ziteh/LEAP/3D_models/Solidworks/下肢/組合/多圈可變電阻定位齒輪組[01-v1.0].SLDASM

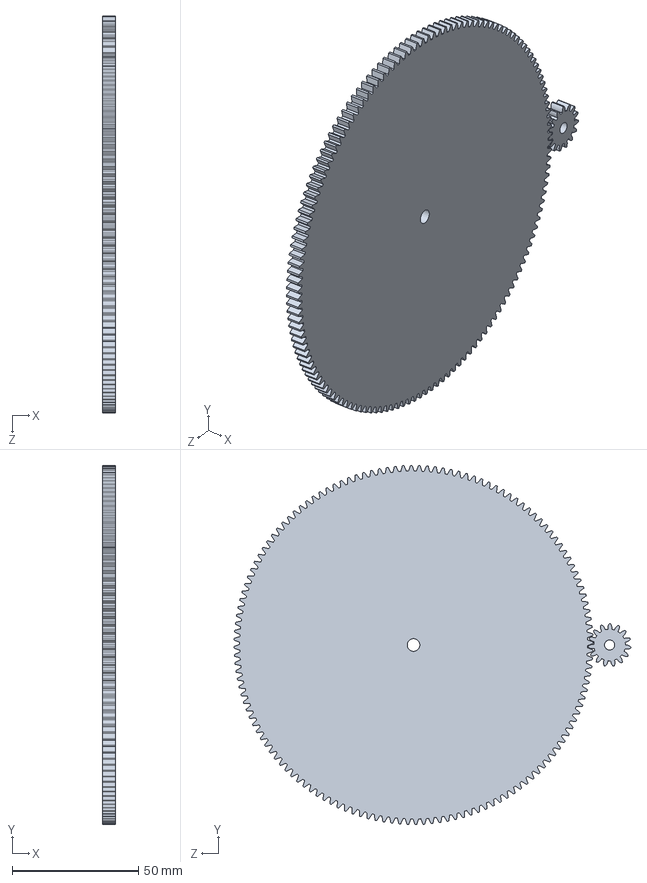
[picture p17: CAD file, 2020-11-13]
3D_models/Solidworks/下肢/組合/多圈可變電阻定位齒輪組[01-v1.0].SLDASM
5.00 x 142.0 x 157.0 mm
spur gear_am x 2
