ziteh/LEAP/3D_models/Solidworks/縮小測試用模型/伺服馬達SG90用轉軸片壓克力固定組合[01-v1.0].SLDASM

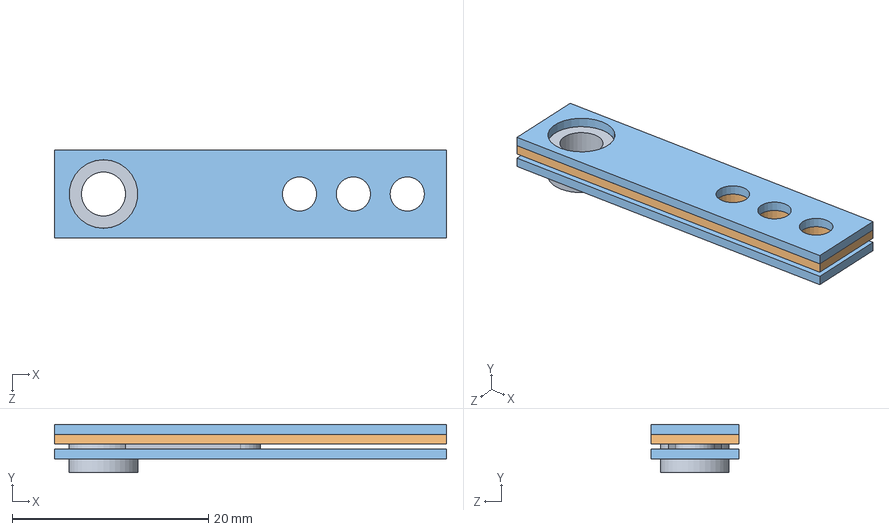
[picture p18: CAD file, 2020-11-13]
3D_models/Solidworks/縮小測試用模型/伺服馬達SG90用轉軸片壓克力固定組合[01-v1.0].SLDASM
40.0 x 4.90 x 9.00 mm
伺服馬達SG90用轉軸片[01-v1.0]
伺服馬達SG90用轉軸片壓克力套[01-v1.0]
伺服馬達SG90用轉軸片壓克力套[02-v1.0] x 2
