ziteh/LEAP/3D_models/Solidworks/下肢/組合/腿部組合-L[01_v3.1(多圈齒輪)].SLDASM

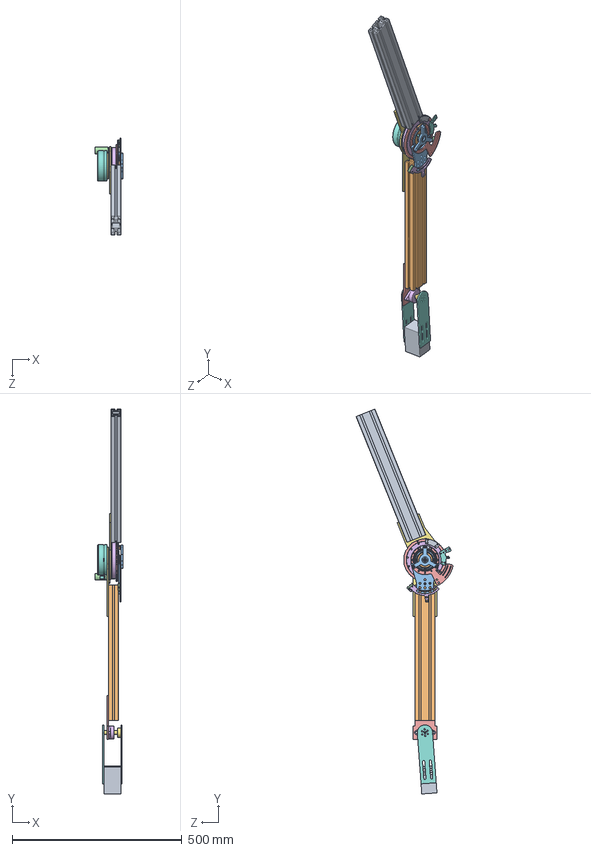
[picture p19: CAD file, 2020-11-13]
3D_models/Solidworks/下肢/組合/腿部組合-L[01_v3.1(多圈齒輪)].SLDASM
81.5 x 1135.4 x 285.7 mm
3060鋁擠型-大腿[01_v1.0]
3060鋁擠型-小腿[01_v1.0]
SHD-2SH_剛性齒輪固定片(01_v2.1)
可變電阻WXD3-13-10KΩ[01-v1.0]
軸承固定座-KFL12固定片[01-v1.0]
軸承固定座-KFL12[01-v1.0]
腳踝軸承軸心固定塊[01_v1.0]
腳踝軸承軸心固定片[01_v1.0] x 2
腳底板固定塊[01_v1.0]
軸承_HD軸向固定(01-v1.0)
HD軸向軸承固定塊(01_v1.0)
HD軸向軸承固定塊(02_v2.0)
多圈可變電阻定位齒輪組-m0.5 250齒[01-v1.0]
多圈可變電阻定位齒輪組-20齒[01-v2.0]
定位多圈可變電阻固定片[01_v5.0]
SHD-2SH_彈性齒杯-可變電阻齒輪固定片[01_v2.0]
SHD-2SH_彈性齒杯-可變電阻齒輪固定片[02_v2.0]
多圈可變電阻定位齒輪固定塊[01-v2.0]
HD軸向軸承固定片(01_v2.0)
微動開關_SS-5GL[01-v1.0] x 2
微動開關(SS-5GL)固定片[01_v2.2]
微動開關(SS-5GL)固定片[02_v2.0]
EC90flot固定片(01_v3.1)
EC90fl-160W-586655
EC90flot軸心固定塊(01_v3.1)
SHD-25-2SH-WG
25 WG BEARING DS
SHD-25-2SH-FS
SHD-25-2SH-CS
SHD-25-2SH-FS2
SHD-2SH_彈性齒杯固定片(01_v4.2)
M4×1[01-v1.0] x 2
HD軸向軸承固定片(03_v1.0)
HD軸向軸承固定片(02_v1.0)
