ziteh/LEAP/3D_models/Solidworks/下肢/組合/氣彈簧組合-01_v1.0.SLDASM

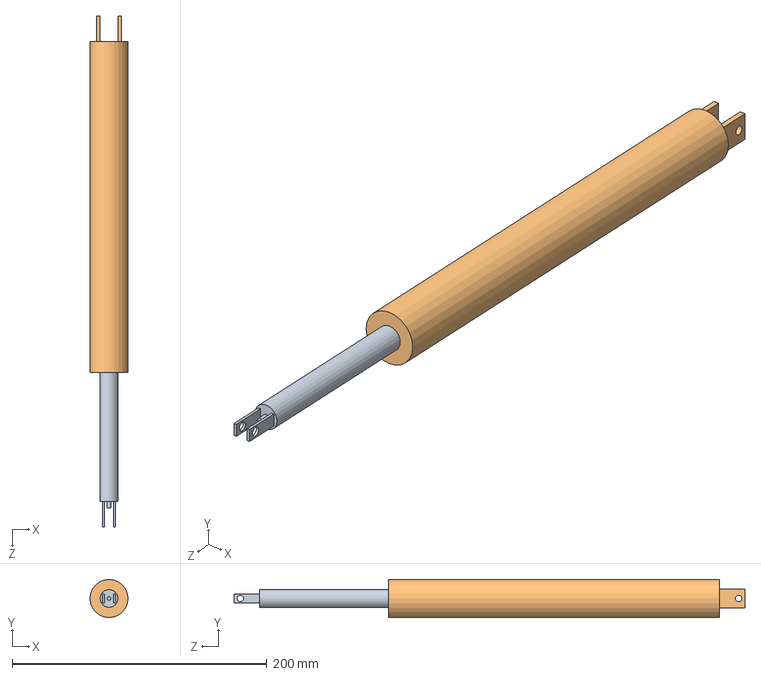
[picture p20: CAD file, 2020-11-13]
3D_models/Solidworks/下肢/組合/氣彈簧組合-01_v1.0.SLDASM
30.0 x 30.0 x 401.6 mm
氣彈簧_伸縮杆-01_v1.0
氣彈簧_缸體-01_v1.0
