ziteh/LEAP/3D_models/Solidworks/下肢/組合/FSR固定片組合[01_v1.0].SLDASM

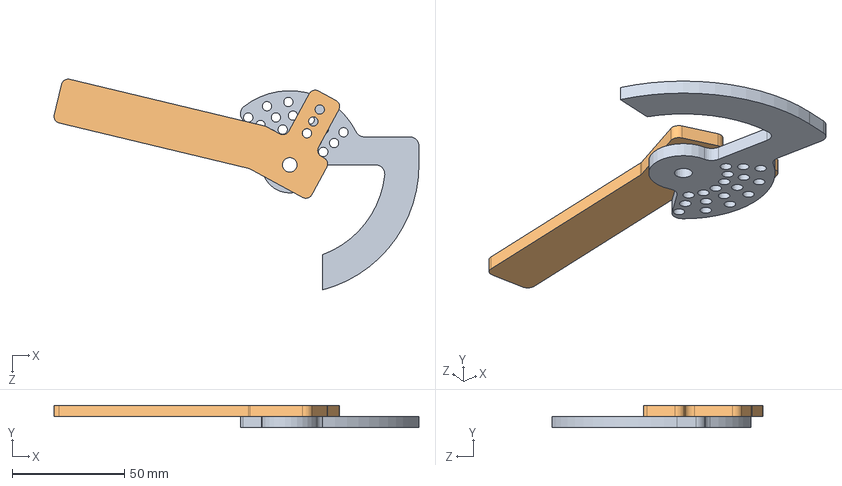
[picture p21: CAD file, 2020-11-13]
3D_models/Solidworks/下肢/組合/FSR固定片組合[01_v1.0].SLDASM
162.4 x 10.0 x 93.8 mm
FSR固定片[02_v4.0]
FSR固定片[01_v4.0]
