ziteh/LEAP/3D_models/Solidworks/縮小測試用模型/定位齒輪[01-v1.0].SLDASM

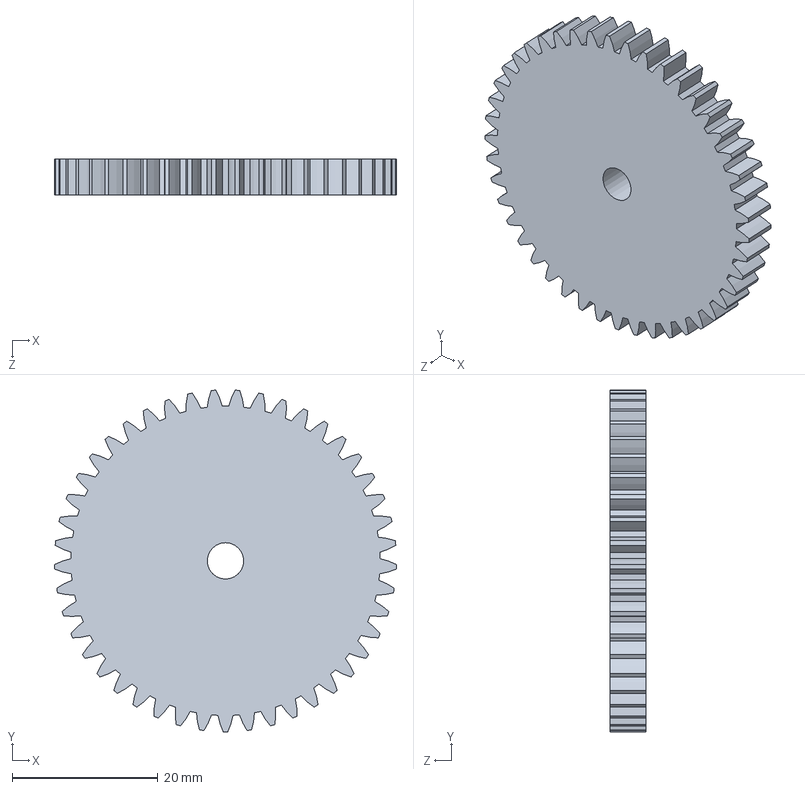
[picture p22: CAD file, 2020-11-13]
3D_models/Solidworks/縮小測試用模型/定位齒輪[01-v1.0].SLDASM
47.0 x 47.0 x 5.00 mm
