ziteh/LEAP/3D_models/Solidworks/下肢/組合/微動開關(SS-5GL)-固定片組合[01_v1.0(伸直)].SLDASM

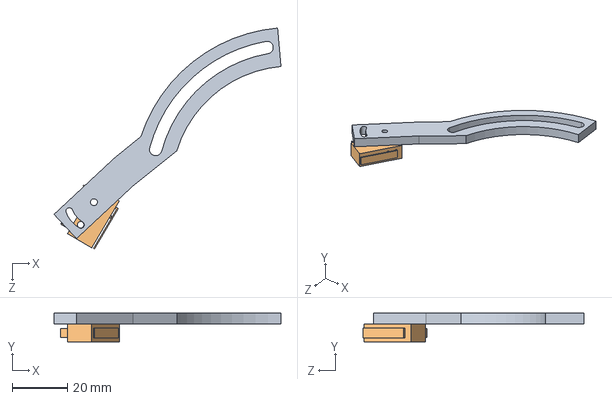
[picture p23: CAD file, 2020-11-13]
3D_models/Solidworks/下肢/組合/微動開關(SS-5GL)-固定片組合[01_v1.0(伸直)].SLDASM
82.4 x 10.4 x 80.2 mm
微動開關(SS-5GL)固定片[01_v1.0]
微動開關_SS-5GL[01-v1.0]
