ziteh/LEAP/3D_models/Solidworks/下肢/組合/諧波減速機(SHF-25-100)組合-01_v1.0.SLDASM

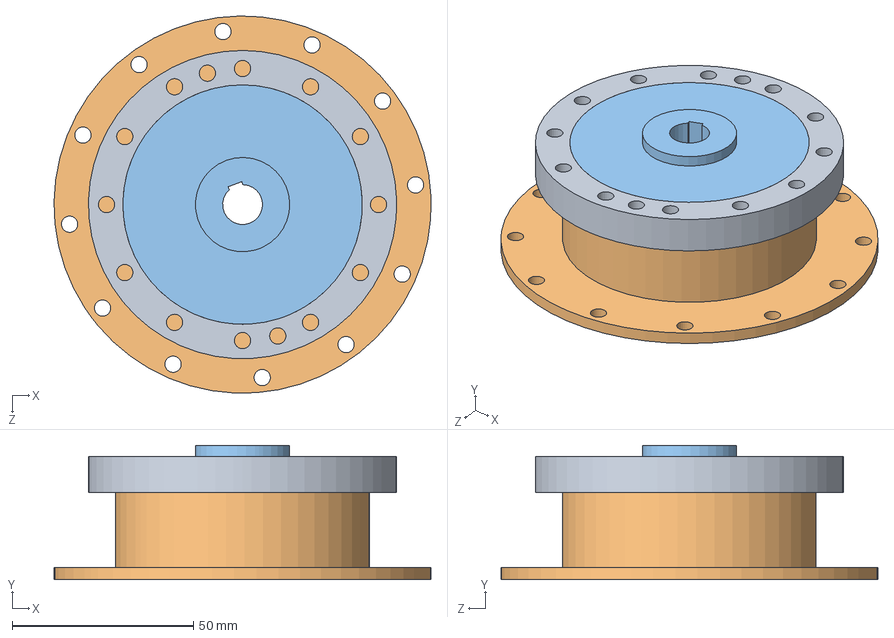
[picture p24: CAD file, 2020-11-13]
3D_models/Solidworks/下肢/組合/諧波減速機(SHF-25-100)組合-01_v1.0.SLDASM
103.9 x 37.0 x 103.9 mm
諧波減速機(SHF-25-100)_剛性齒輪-01_v1.0
諧波減速機(SHF-25-100)_彈性齒杯-01_v1.0
諧波減速機(SHF-25-100)_波產生器-01_v1.0
