ziteh/LEAP/3D_models/Inventor/鋁擠型/3060鋁擠型(Prototype)-01_v1.DXF

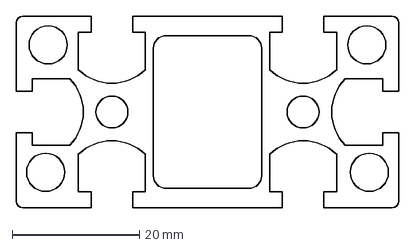
[picture p25: CAD file, 2020-11-13]
3D_models/Inventor/鋁擠型/3060鋁擠型(Prototype)-01_v1.DXF
60.0 x 30.0 mm
