ziteh/LEAP/3D_models/Solidworks/下肢/Others/腳踝部[01-v1.0].SLDPRT

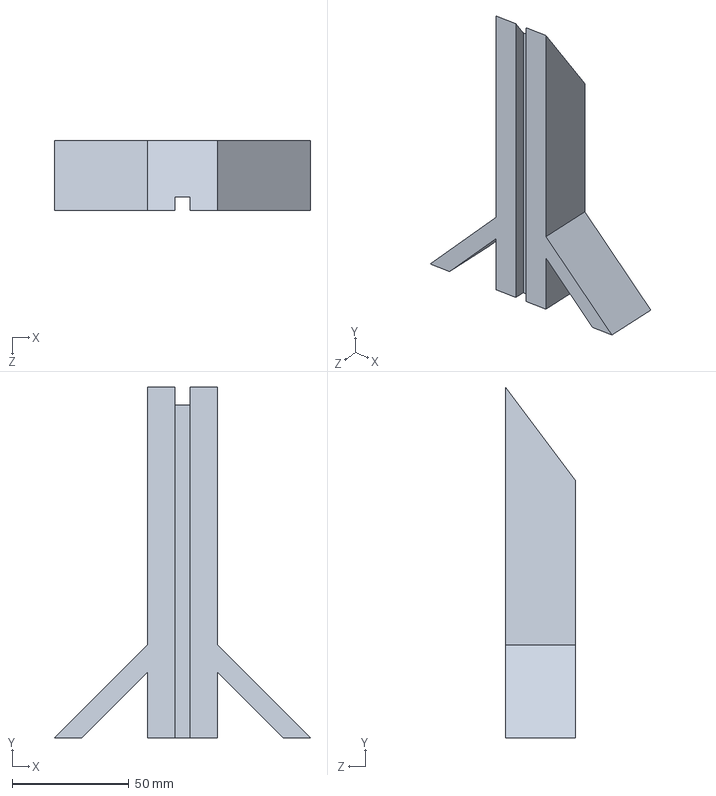
[picture p26: CAD file, 2020-11-14]
3D_models/Solidworks/下肢/Others/腳踝部[01-v1.0].SLDPRT
109.5 x 150.0 x 30.0 mm
