ziteh/LEAP/3D_models/Solidworks/下肢/固定-標準/M4×1[01-v1.0].SLDPRT

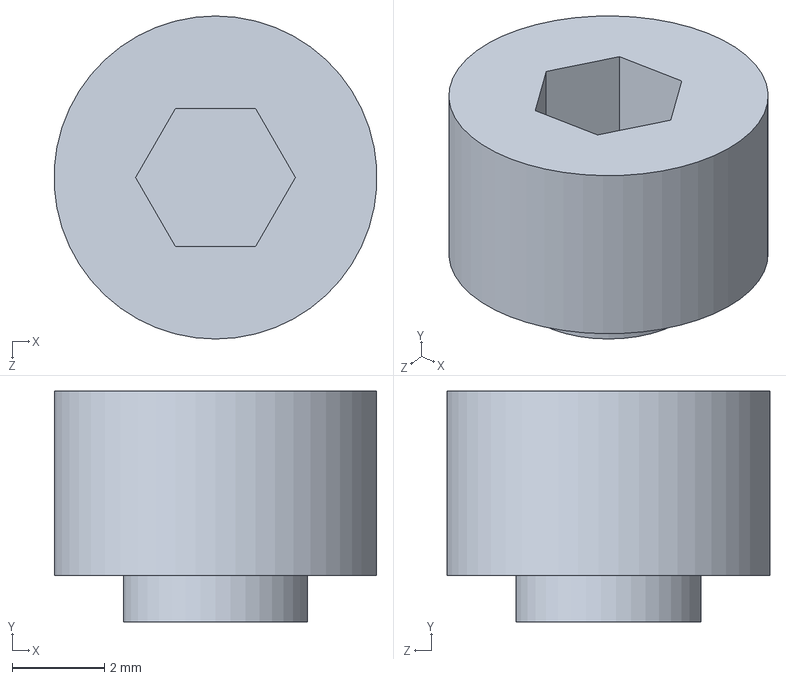
[picture p27: CAD file, 2020-11-14]
3D_models/Solidworks/下肢/固定-標準/M4×1[01-v1.0].SLDPRT
6.99 x 5.00 x 7.00 mm
