ziteh/LEAP/3D_models/Solidworks/下肢/機械/SHD-2SH/SHD-25-2SH-CS.sldprt

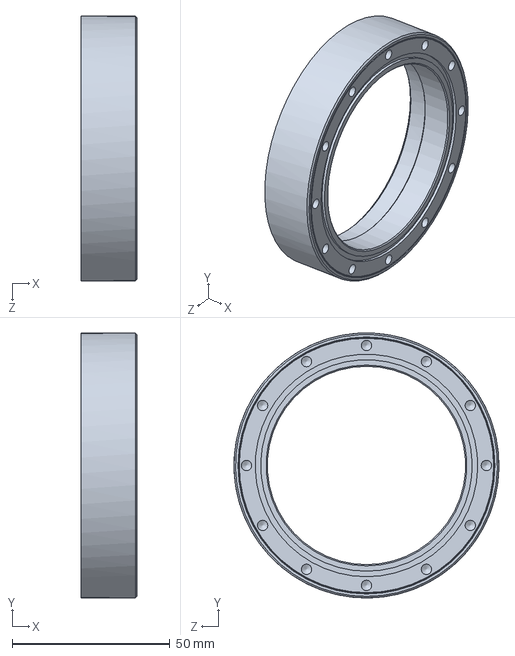
[picture p28: CAD file, 2020-11-14]
3D_models/Solidworks/下肢/機械/SHD-2SH/SHD-25-2SH-CS.sldprt
17.7 x 84.0 x 84.0 mm
