ziteh/LEAP/3D_models/Solidworks/下肢/機械/軸承_HD軸向固定(01-v1.0).SLDPRT

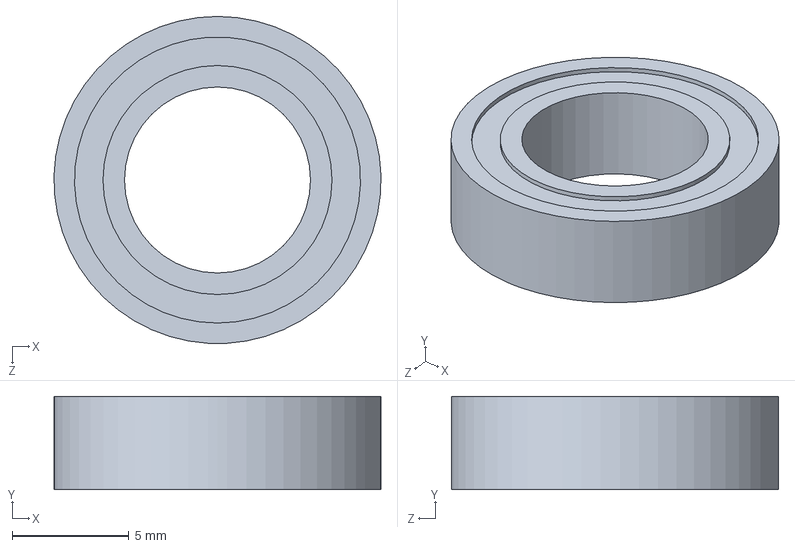
[picture p29: CAD file, 2020-11-14]
3D_models/Solidworks/下肢/機械/軸承_HD軸向固定(01-v1.0).SLDPRT
14.0 x 4.00 x 14.0 mm
