ziteh/LEAP/3D_models/Solidworks/下肢/鋁擠型/3060鋁擠型-大腿[01_v1.0].SLDPRT

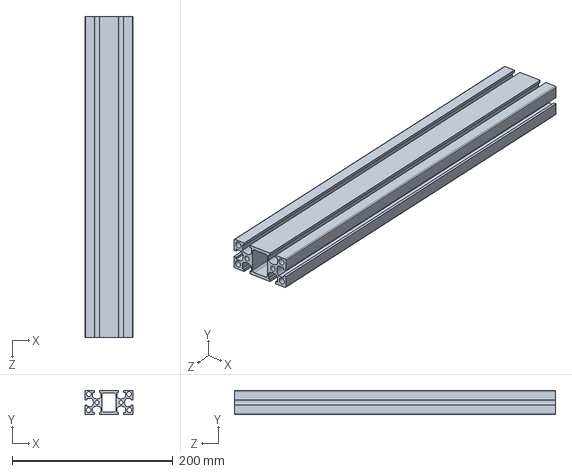
[picture p30: CAD file, 2020-11-14]
3D_models/Solidworks/下肢/鋁擠型/3060鋁擠型-大腿[01_v1.0].SLDPRT
60.0 x 30.0 x 400.0 mm
