ziteh/LEAP/3D_models/Solidworks/下肢/電子電機/EC90fl-160W-586655.SLDPRT

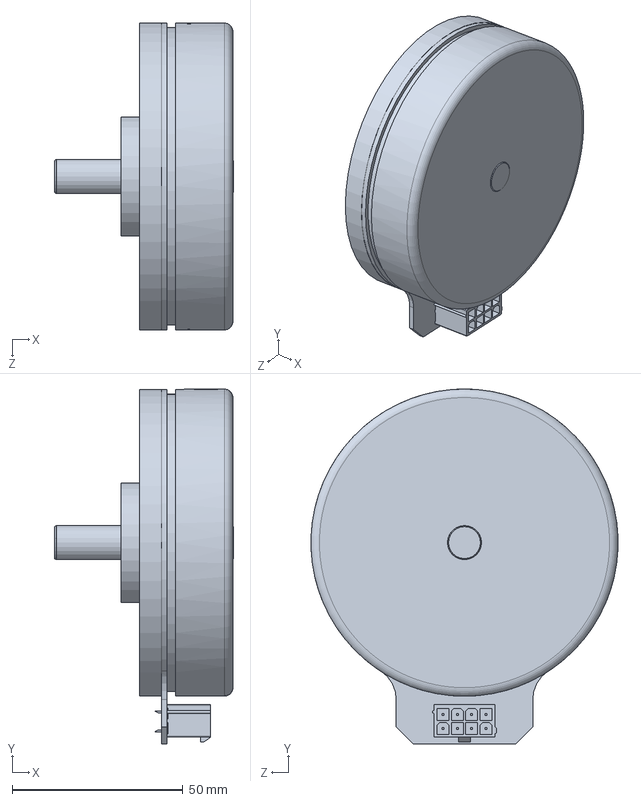
[picture p31: CAD file, 2020-11-14]
3D_models/Solidworks/下肢/電子電機/EC90fl-160W-586655.SLDPRT
52.5 x 104.0 x 90.0 mm
