ziteh/LEAP/3D_models/Solidworks/縮小測試用模型/伺服馬達SG90[01-v1.0].SLDPRT

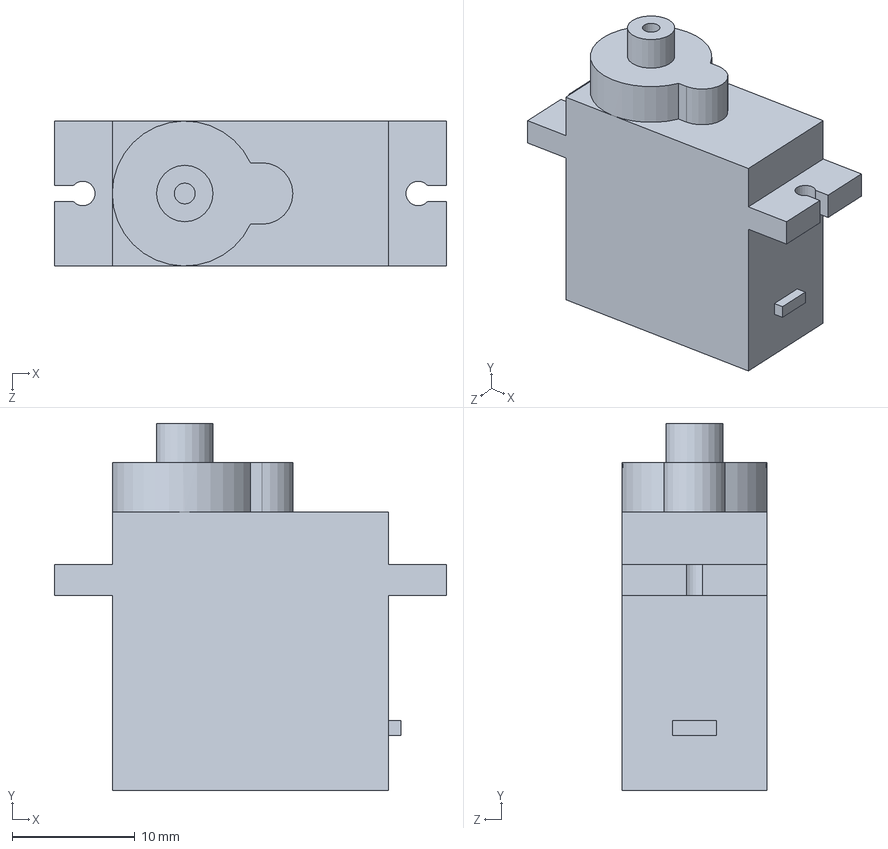
[picture p32: CAD file, 2020-11-13]
3D_models/Solidworks/縮小測試用模型/伺服馬達SG90[01-v1.0].SLDPRT
31.9 x 29.9 x 11.8 mm
