ziteh/LEAP/3D_models/Solidworks/縮小測試用模型v2/Export/小腿板[01-v1.DXF

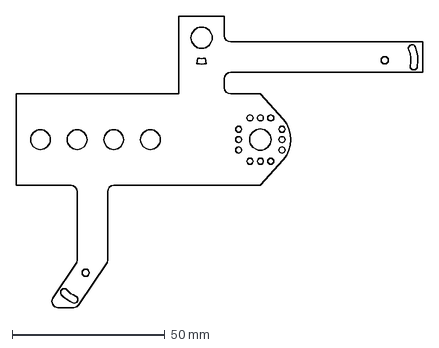
[picture p33: CAD file, 2020-11-13]
3D_models/Solidworks/縮小測試用模型v2/Export/小腿板[01-v1.DXF
133.2 x 95.3 mm
