ziteh/LEAP/3D_models/Solidworks/縮小測試用模型v2/大腿副齒輪[01-v1.0].SLDPRT

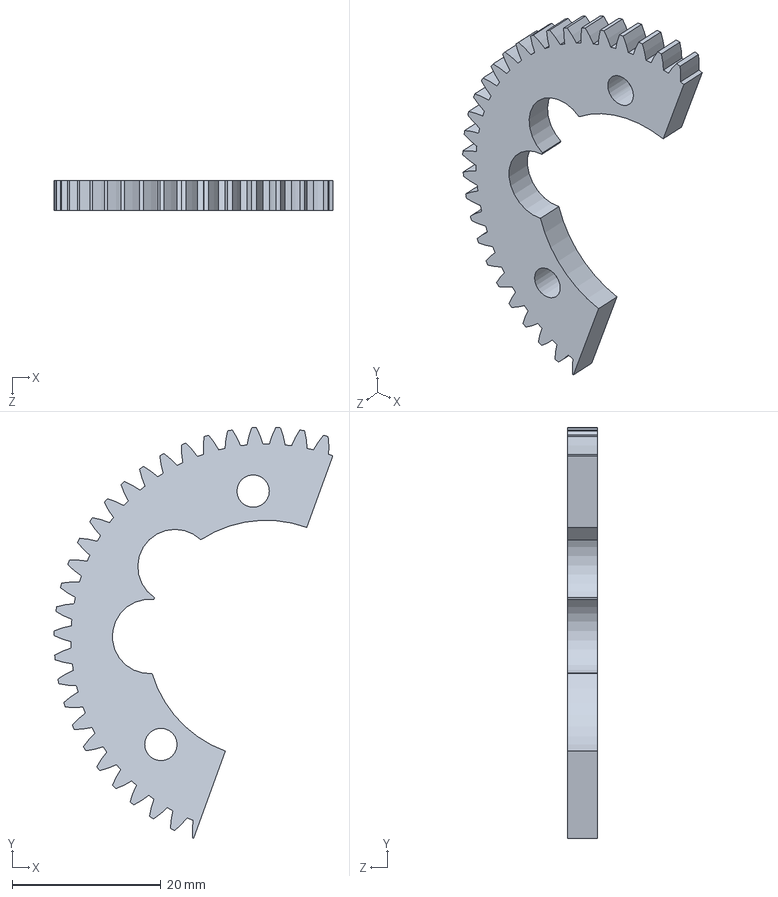
[picture p34: CAD file, 2020-11-13]
3D_models/Solidworks/縮小測試用模型v2/大腿副齒輪[01-v1.0].SLDPRT
37.5 x 55.3 x 4.00 mm
