ziteh/LEAP/3D_models/Solidworks/下肢/Others/編碼器大齒輪[01-v2.0].SLDPRT

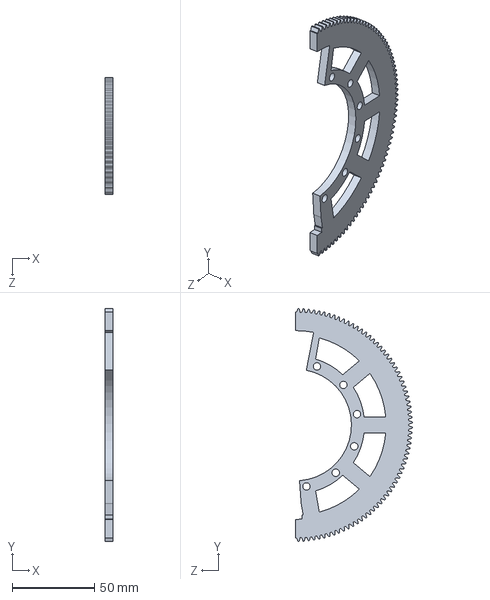
[picture p35: CAD file, 2020-11-13]
3D_models/Solidworks/下肢/Others/編碼器大齒輪[01-v2.0].SLDPRT
5.00 x 142.0 x 71.1 mm
