ziteh/LEAP/3D_models/Solidworks/下肢/固定-標準/3030鋁擠型三角件M6[01-v1.0].SLDPRT

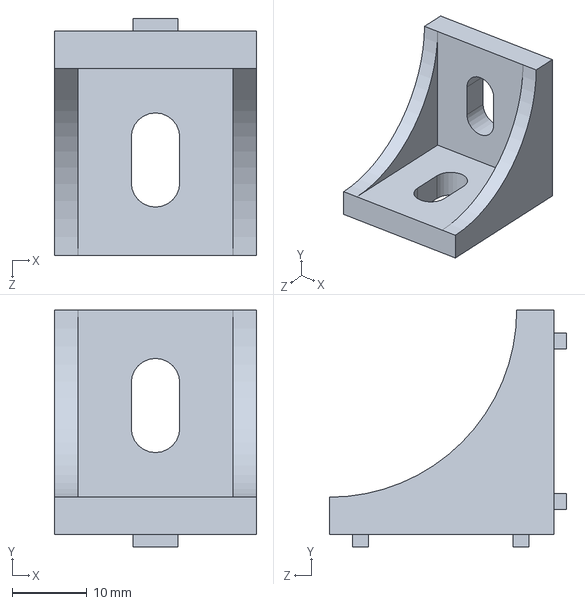
[picture p36: CAD file, 2020-11-14]
3D_models/Solidworks/下肢/固定-標準/3030鋁擠型三角件M6[01-v1.0].SLDPRT
27.0 x 31.6 x 31.6 mm
