ziteh/LEAP/3D_models/Solidworks/下肢/固定/HD軸向軸承固定塊(02_v2.0).SLDPRT

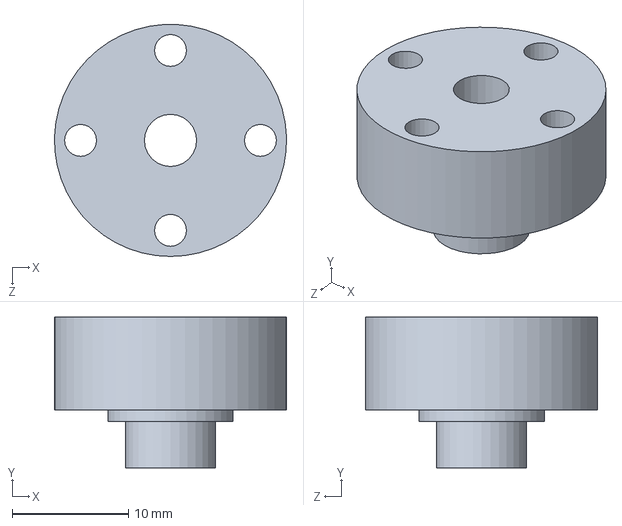
[picture p37: CAD file, 2020-11-14]
3D_models/Solidworks/下肢/固定/HD軸向軸承固定塊(02_v2.0).SLDPRT
20.0 x 13.0 x 20.0 mm
