ziteh/LEAP/3D_models/Solidworks/下肢/機械/SHD-2SH/SHD-25-2SH-FS2.sldprt

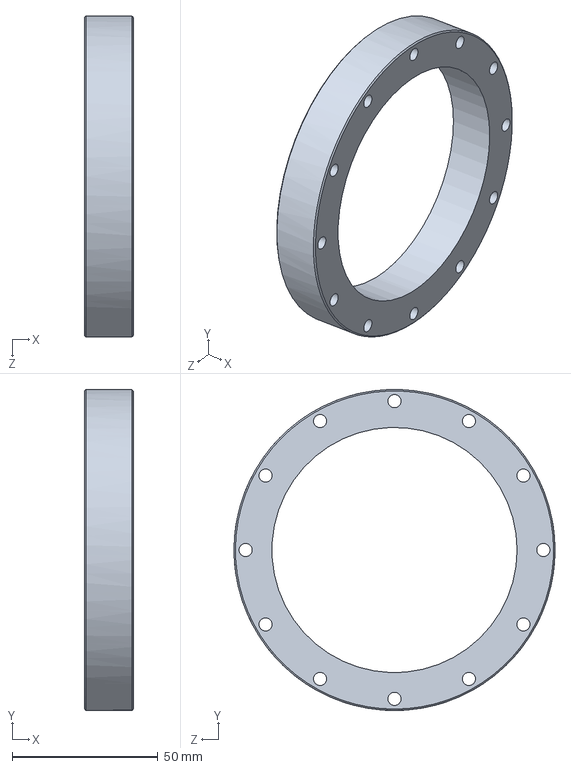
[picture p38: CAD file, 2020-11-14]
3D_models/Solidworks/下肢/機械/SHD-2SH/SHD-25-2SH-FS2.sldprt
16.7 x 110.0 x 110.0 mm
