ziteh/LEAP/3D_models/Solidworks/下肢/機械/多圈可變電阻定位齒輪組/多圈可變電阻定位齒輪組-m0.5 250齒[01-v1.0].SLDPRT

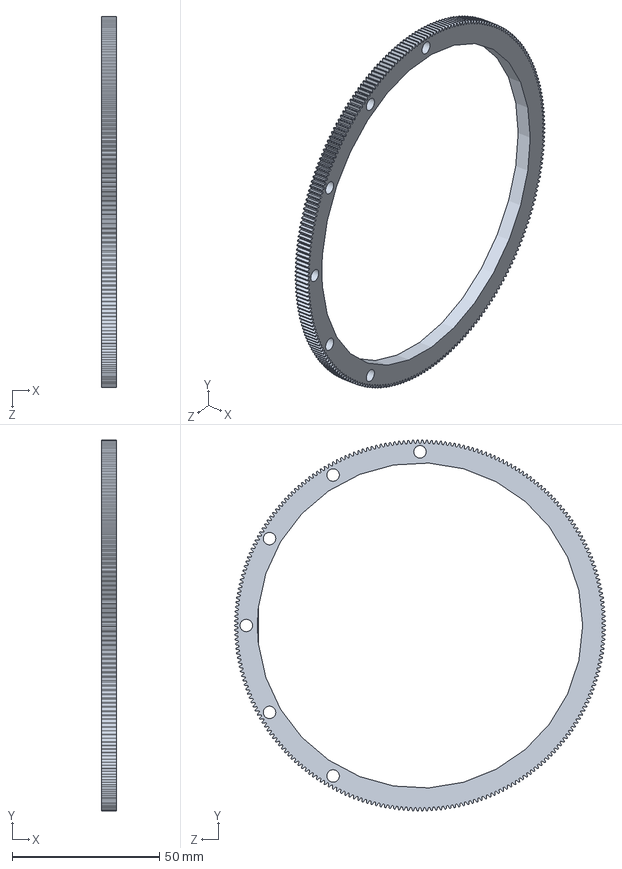
[picture p39: CAD file, 2020-11-14]
3D_models/Solidworks/下肢/機械/多圈可變電阻定位齒輪組/多圈可變電阻定位齒輪組-m0.5 250齒[01-v1.0].SLDPRT
5.00 x 126.0 x 126.0 mm
