ziteh/LEAP/3D_models/Solidworks/下肢/機械/軸承固定座-FL04-5[01-v1.0].SLDPRT

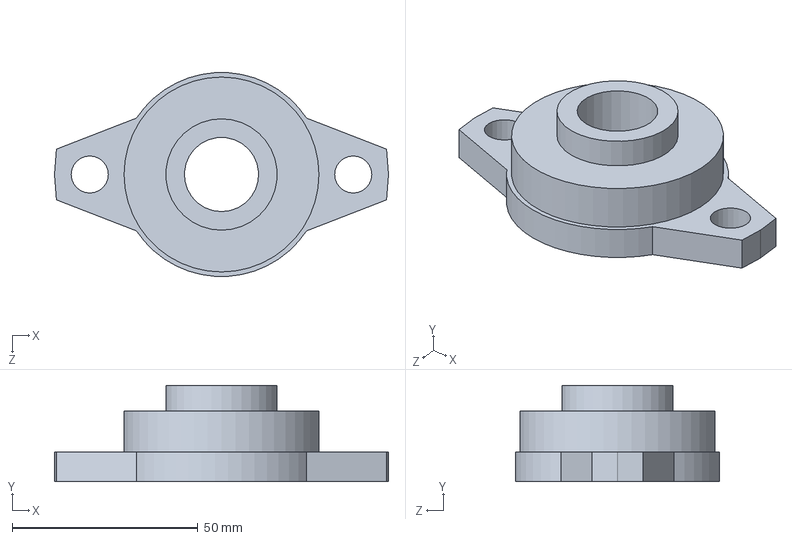
[picture p40: CAD file, 2020-11-14]
3D_models/Solidworks/下肢/機械/軸承固定座-FL04-5[01-v1.0].SLDPRT
90.0 x 26.0 x 54.9 mm
