ziteh/LEAP/3D_models/Solidworks/下肢/電子電機/可變電阻WXD3-13-10KΩ[01-v1.0].SLDPRT

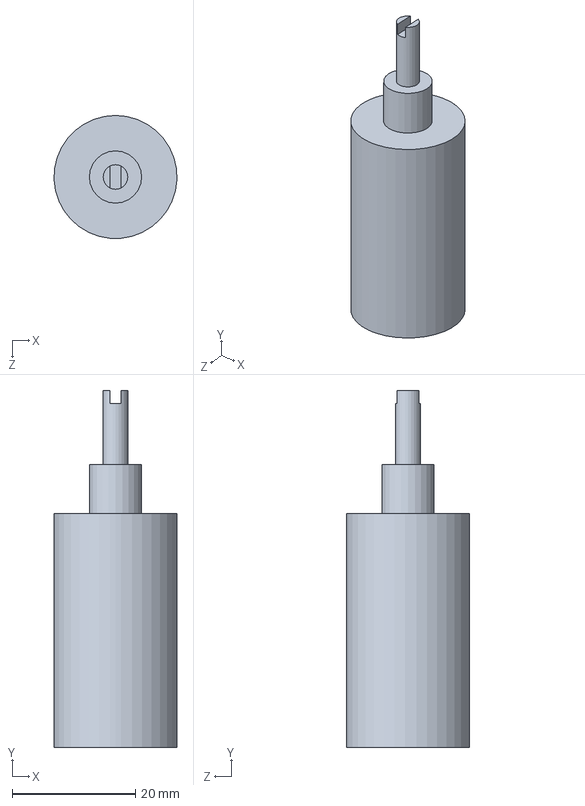
[picture p41: CAD file, 2020-11-14]
3D_models/Solidworks/下肢/電子電機/可變電阻WXD3-13-10KΩ[01-v1.0].SLDPRT
20.0 x 58.0 x 20.0 mm
