ziteh/LEAP/3D_models/Solidworks/縮小測試用模型/可變電阻齒輪[01-v2.1].DXF

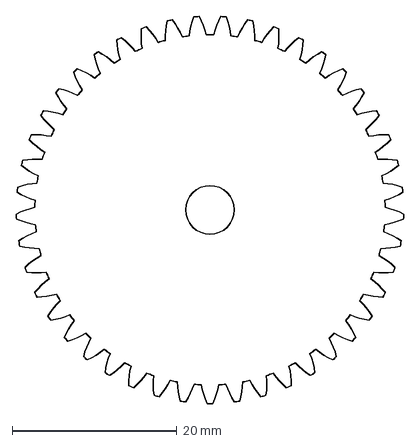
[picture p42: CAD file, 2020-11-13]
3D_models/Solidworks/縮小測試用模型/可變電阻齒輪[01-v2.1].DXF
47.0 x 47.0 mm
