ziteh/LEAP/3D_models/Solidworks/縮小測試用模型v2/Export/大腿副齒輪[01-v1.DXF

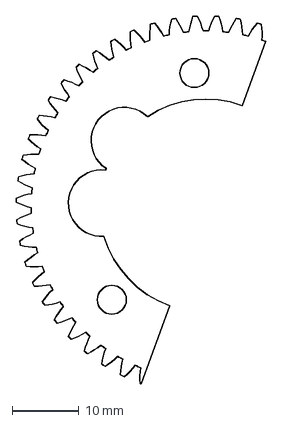
[picture p43: CAD file, 2020-11-13]
3D_models/Solidworks/縮小測試用模型v2/Export/大腿副齒輪[01-v1.DXF
37.5 x 55.3 mm
