ziteh/LEAP/3D_models/Solidworks/縮小測試用模型v2/MG996R_固定盤[01-v1.0].SLDPRT

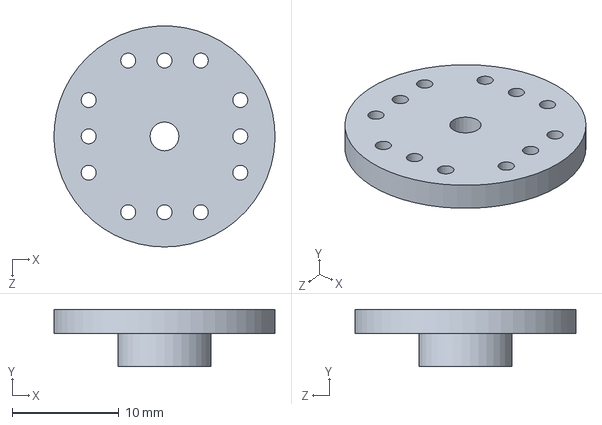
[picture p44: CAD file, 2020-11-13]
3D_models/Solidworks/縮小測試用模型v2/MG996R_固定盤[01-v1.0].SLDPRT
20.7 x 5.38 x 20.7 mm
