ziteh/LEAP/3D_models/Solidworks/下肢/固定-標準/M6鋁擠型螺絲母[01-v1.0].SLDPRT

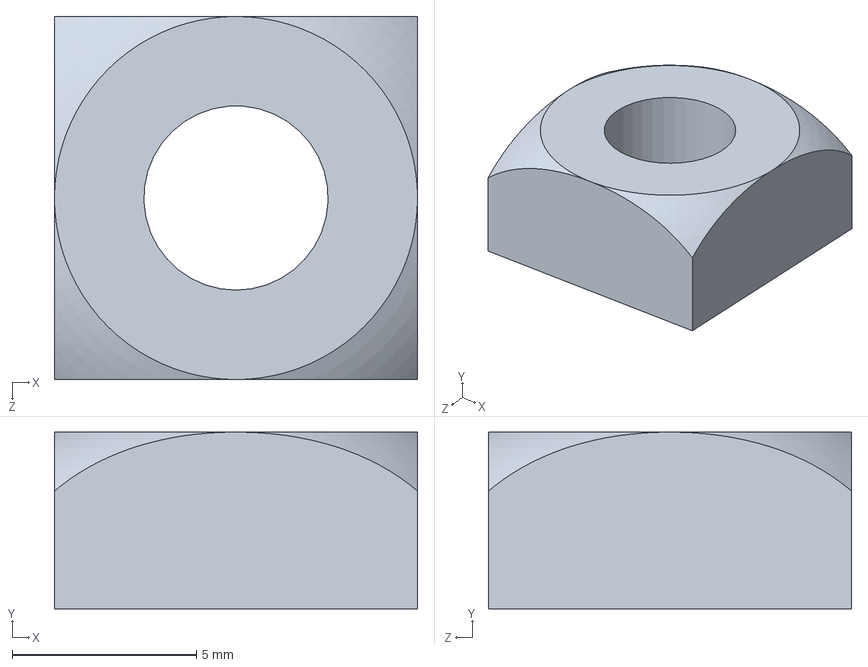
[picture p45: CAD file, 2020-11-13]
3D_models/Solidworks/下肢/固定-標準/M6鋁擠型螺絲母[01-v1.0].SLDPRT
9.85 x 4.80 x 9.85 mm
