ziteh/LEAP/3D_models/Solidworks/下肢/固定/HD軸向軸承固定片(03_v1.0).SLDPRT

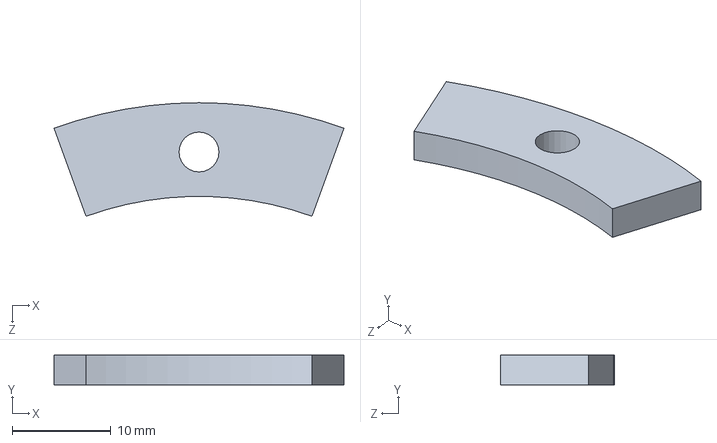
[picture p46: CAD file, 2020-11-14]
3D_models/Solidworks/下肢/固定/HD軸向軸承固定片(03_v1.0).SLDPRT
29.4 x 3.00 x 11.5 mm
