ziteh/LEAP/3D_models/Solidworks/下肢/機械/多圈可變電阻定位齒輪組/多圈可變電阻定位齒輪組-20齒[01-v2.0].SLDPRT

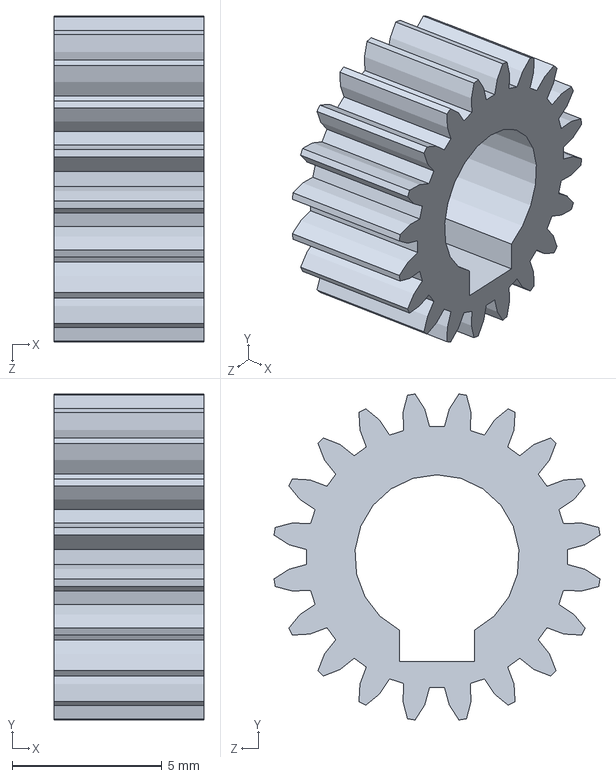
[picture p47: CAD file, 2020-11-14]
3D_models/Solidworks/下肢/機械/多圈可變電阻定位齒輪組/多圈可變電阻定位齒輪組-20齒[01-v2.0].SLDPRT
5.00 x 10.9 x 10.9 mm
