ziteh/LEAP/3D_models/Solidworks/下肢/機械/軸承固定座-KFL12[01-v1.0].SLDPRT

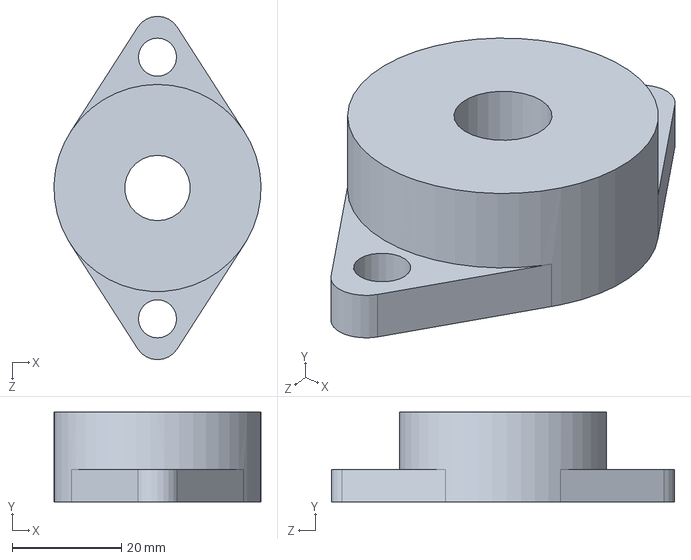
[picture p48: CAD file, 2020-11-14]
3D_models/Solidworks/下肢/機械/軸承固定座-KFL12[01-v1.0].SLDPRT
38.0 x 16.5 x 63.0 mm
