ziteh/LEAP/3D_models/Solidworks/下肢/電子電機/微動開關_SS-5GL[01-v1.0].SLDPRT

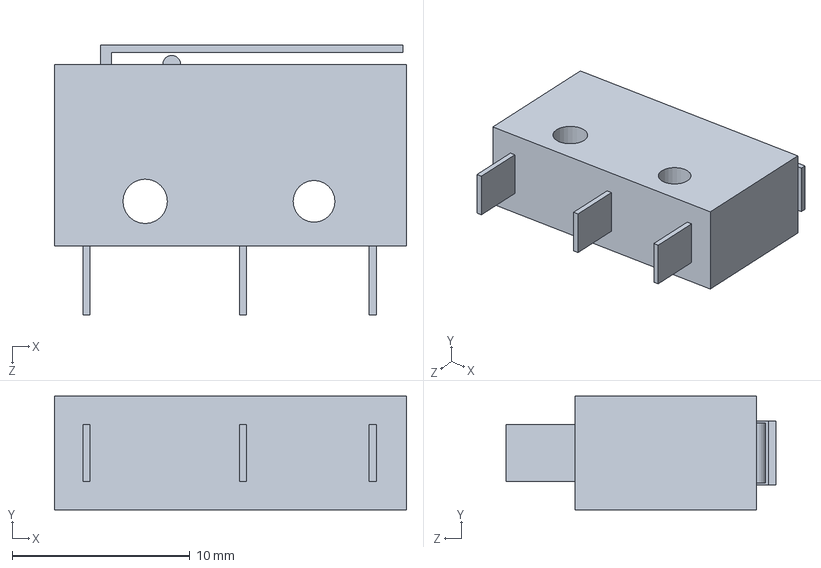
[picture p49: CAD file, 2020-11-14]
3D_models/Solidworks/下肢/電子電機/微動開關_SS-5GL[01-v1.0].SLDPRT
19.8 x 6.40 x 15.2 mm
