ziteh/LEAP/3D_models/Solidworks/縮小測試用模型v2/Export/大腿板[01-v2.DXF

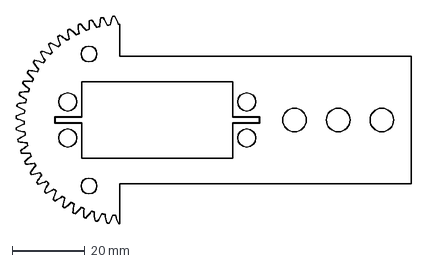
[picture p50: CAD file, 2020-11-13]
3D_models/Solidworks/縮小測試用模型v2/Export/大腿板[01-v2.DXF
108.5 x 57.0 mm
