ziteh/LEAP/3D_models/Solidworks/下肢/固定-標準/M6×16[01-v1.0].SLDPRT

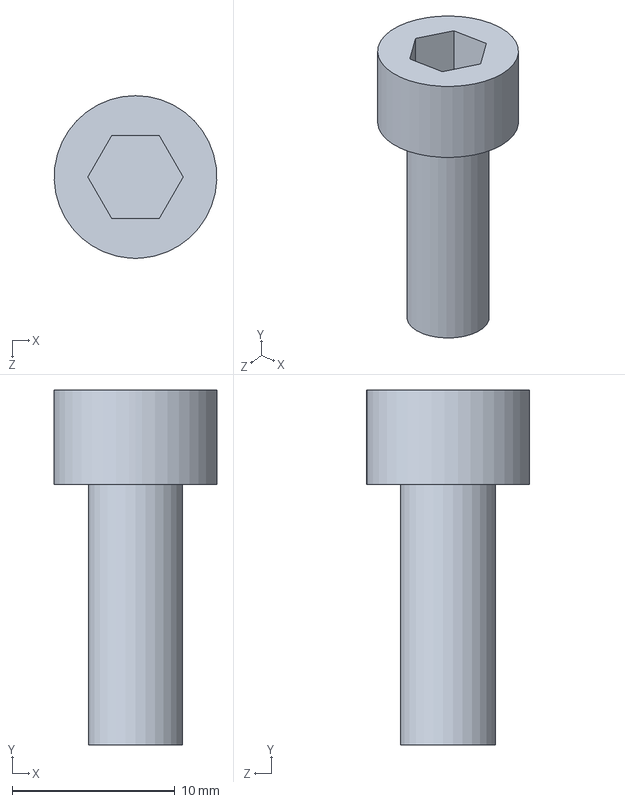
[picture p51: CAD file, 2020-11-13]
3D_models/Solidworks/下肢/固定-標準/M6×16[01-v1.0].SLDPRT
9.99 x 21.8 x 10.0 mm
