ziteh/LEAP/3D_models/Solidworks/下肢/固定/腳踝軸承軸心固定板[01_v1.0].SLDPRT

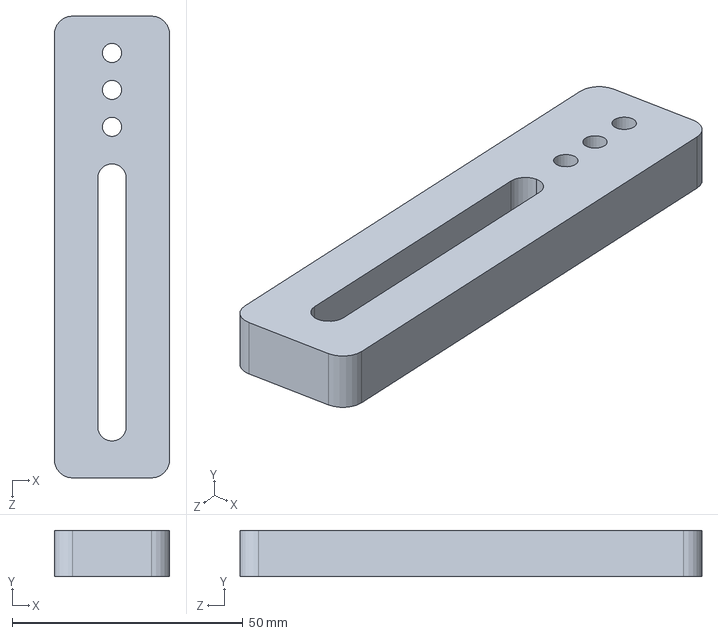
[picture p52: CAD file, 2020-11-14]
3D_models/Solidworks/下肢/固定/腳踝軸承軸心固定板[01_v1.0].SLDPRT
25.0 x 10.0 x 100.0 mm
