ziteh/LEAP/3D_models/Solidworks/下肢/機械/多圈可變電阻定位齒輪組/多圈可變電阻定位齒輪固定塊[01-v3.0].SLDPRT

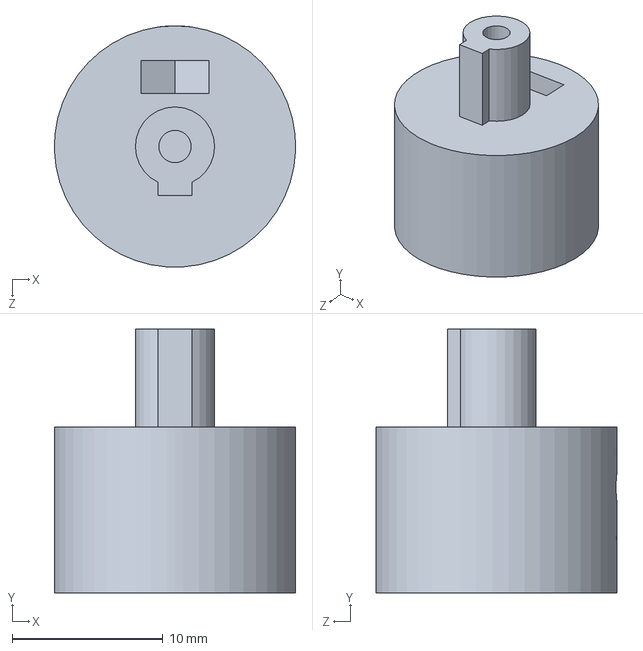
[picture p53: CAD file, 2020-11-14]
3D_models/Solidworks/下肢/機械/多圈可變電阻定位齒輪組/多圈可變電阻定位齒輪固定塊[01-v3.0].SLDPRT
16.0 x 17.5 x 16.0 mm
