ziteh/LEAP/3D_models/Solidworks/下肢/機械/軸承(SKF單列圓柱滾子20)_滾子-01_v1.0.SLDPRT

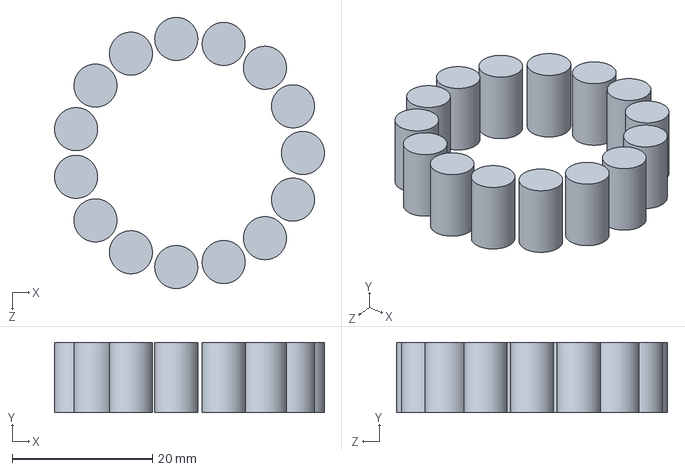
[picture p54: CAD file, 2020-11-13]
3D_models/Solidworks/下肢/機械/軸承(SKF單列圓柱滾子20)_滾子-01_v1.0.SLDPRT
38.4 x 10.0 x 38.6 mm
