ziteh/LEAP/3D_models/Solidworks/下肢/電子電機/FSR[01-v1.0].SLDPRT

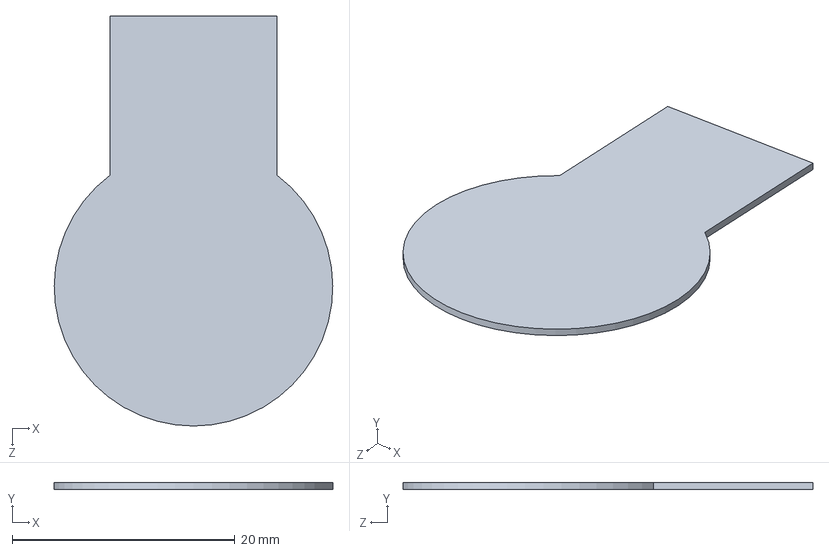
[picture p55: CAD file, 2020-11-14]
3D_models/Solidworks/下肢/電子電機/FSR[01-v1.0].SLDPRT
25.0 x 0.6 x 36.8 mm
