ziteh/LEAP/3D_models/Solidworks/縮小測試用模型/可變電阻[01-v1.0].SLDPRT

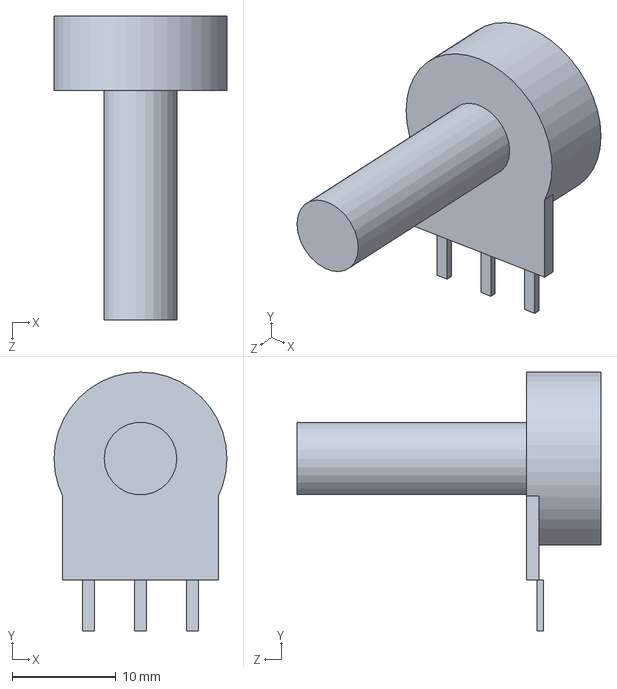
[picture p56: CAD file, 2020-11-13]
3D_models/Solidworks/縮小測試用模型/可變電阻[01-v1.0].SLDPRT
16.7 x 24.9 x 29.3 mm
