ziteh/LEAP/3D_models/Solidworks/縮小測試用模型v2/大腿板[01-v2.0].SLDPRT

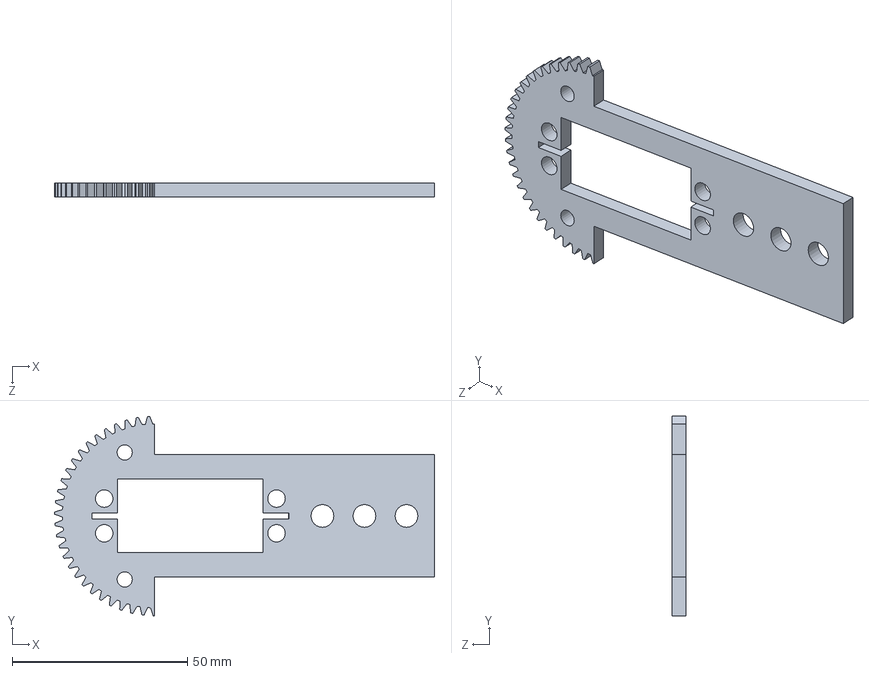
[picture p57: CAD file, 2020-11-13]
3D_models/Solidworks/縮小測試用模型v2/大腿板[01-v2.0].SLDPRT
108.5 x 57.0 x 4.00 mm
