ziteh/LEAP/3D_models/Solidworks/下肢/Others/腳底板-01_v1.0.SLDPRT

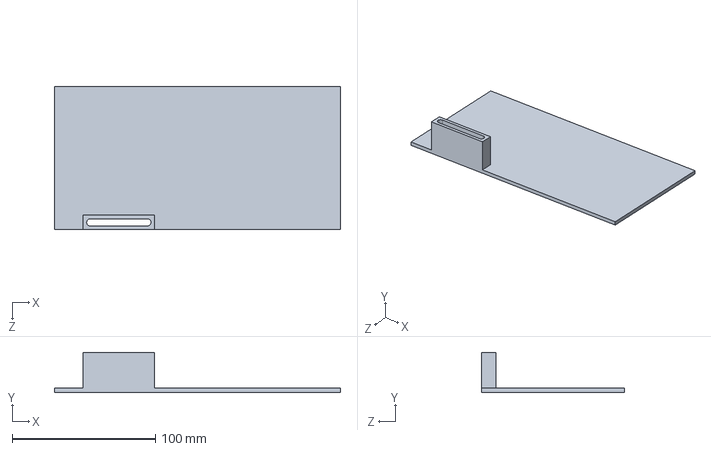
[picture p58: CAD file, 2020-11-13]
3D_models/Solidworks/下肢/Others/腳底板-01_v1.0.SLDPRT
200.0 x 28.0 x 100.0 mm
