ziteh/LEAP/3D_models/Solidworks/下肢/固定/小腿固定片[01_v2.0].SLDPRT

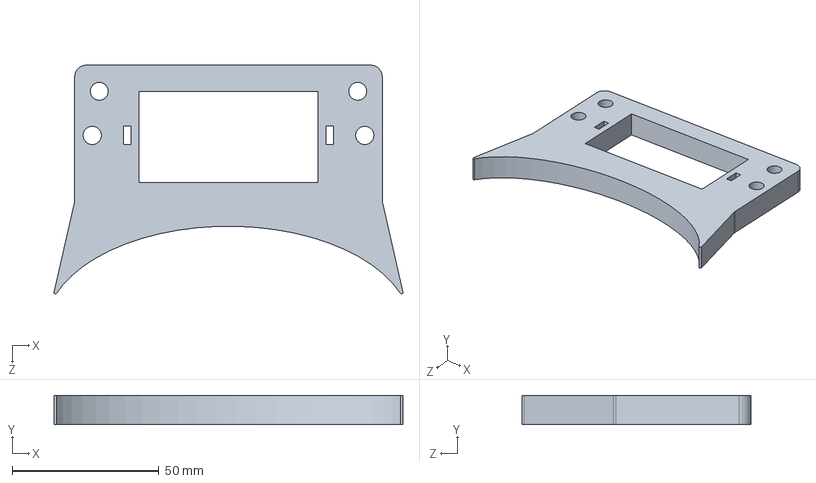
[picture p59: CAD file, 2020-11-14]
3D_models/Solidworks/下肢/固定/小腿固定片[01_v2.0].SLDPRT
119.1 x 10.0 x 78.1 mm
