ziteh/LEAP/3D_models/Solidworks/下肢/機械/多圈可變電阻定位齒輪組/多圈可變電阻定位齒輪組-140齒[01-v1.0].SLDPRT

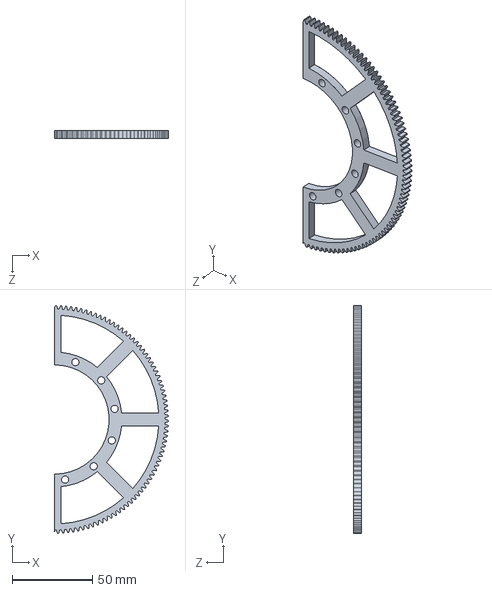
[picture p60: CAD file, 2020-11-13]
3D_models/Solidworks/下肢/機械/多圈可變電阻定位齒輪組/多圈可變電阻定位齒輪組-140齒[01-v1.0].SLDPRT
71.0 x 142.0 x 5.00 mm
