ziteh/LEAP/3D_models/Solidworks/下肢/電子電機/微動開關_TMV101-C[01-v1.0].SLDPRT

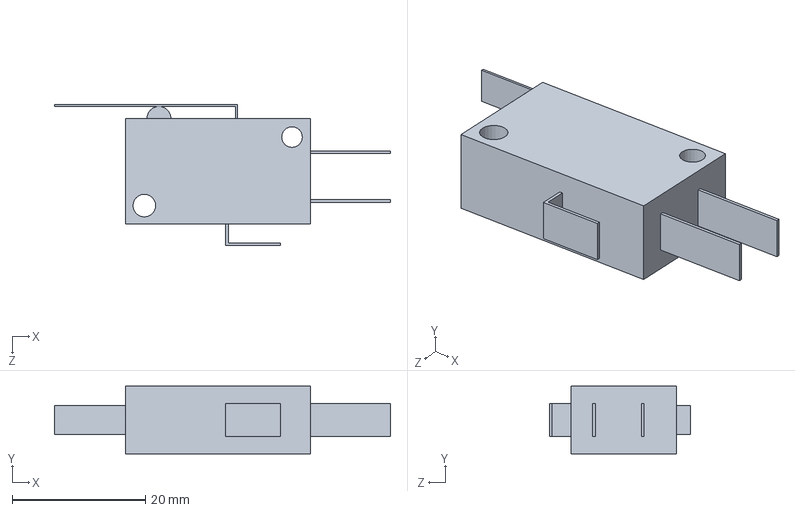
[picture p62: CAD file, 2020-11-13]
3D_models/Solidworks/下肢/電子電機/微動開關_TMV101-C[01-v1.0].SLDPRT
50.5 x 10.2 x 21.2 mm
