ziteh/LEAP/3D_models/Solidworks/縮小測試用模型/伺服馬達SG90固定板-大腿[01-v1.0].SLDPRT

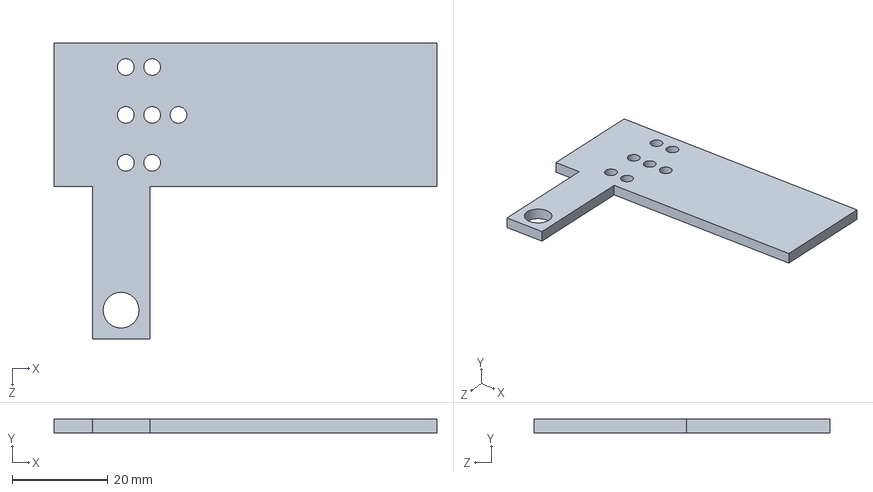
[picture p63: CAD file, 2020-11-13]
3D_models/Solidworks/縮小測試用模型/伺服馬達SG90固定板-大腿[01-v1.0].SLDPRT
80.0 x 3.00 x 61.8 mm
