ziteh/LEAP/3D_models/Solidworks/縮小測試用模型v2/Export/齒輪[02-v1.1DXF.DXF

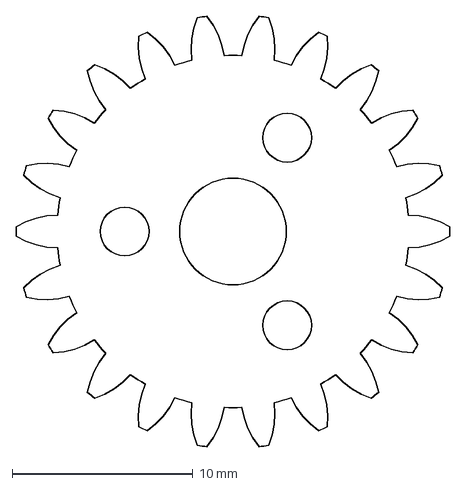
[picture p64: CAD file, 2020-11-13]
3D_models/Solidworks/縮小測試用模型v2/Export/齒輪[02-v1.1DXF.DXF
24.0 x 23.8 mm
