ziteh/LEAP/3D_models/Solidworks/縮小測試用模型v2/可變電阻[01-v1.0].SLDPRT

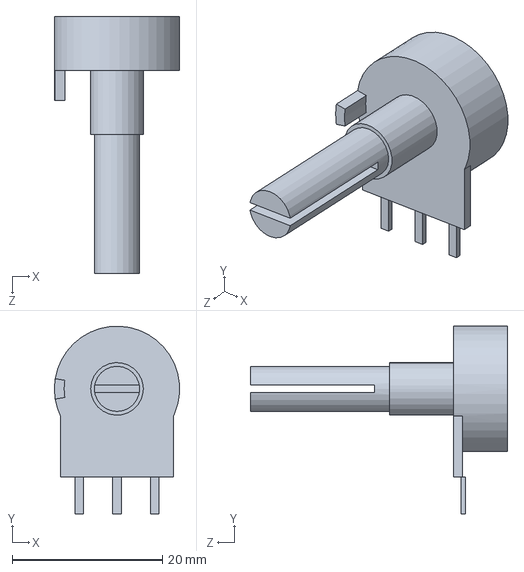
[picture p65: CAD file, 2020-11-13]
3D_models/Solidworks/縮小測試用模型v2/可變電阻[01-v1.0].SLDPRT
16.7 x 24.9 x 34.2 mm
