ziteh/LEAP/3D_models/Solidworks/下肢/Others/編碼器大同步輪[01-v1.0].SLDPRT

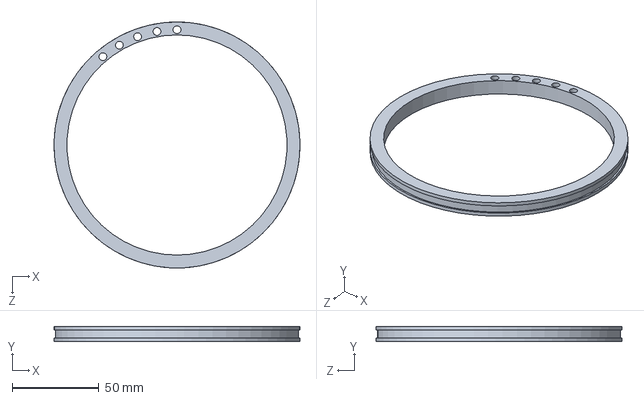
[picture p66: CAD file, 2020-11-13]
3D_models/Solidworks/下肢/Others/編碼器大同步輪[01-v1.0].SLDPRT
141.9 x 8.50 x 142.0 mm
