ziteh/LEAP/3D_models/Solidworks/下肢/固定/FSR固定片[01_v4.0].SLDPRT

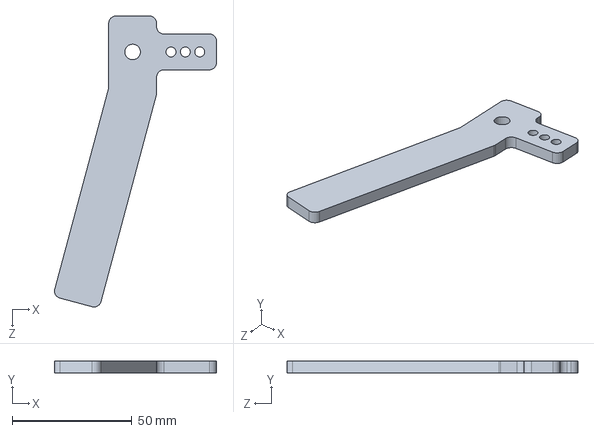
[picture p67: CAD file, 2020-11-14]
3D_models/Solidworks/下肢/固定/FSR固定片[01_v4.0].SLDPRT
67.6 x 5.00 x 121.4 mm
