ziteh/LEAP/3D_models/Solidworks/下肢/機械/SHD-2SH/SHD-25-100-2SH(01-v1.0).SLDPRT

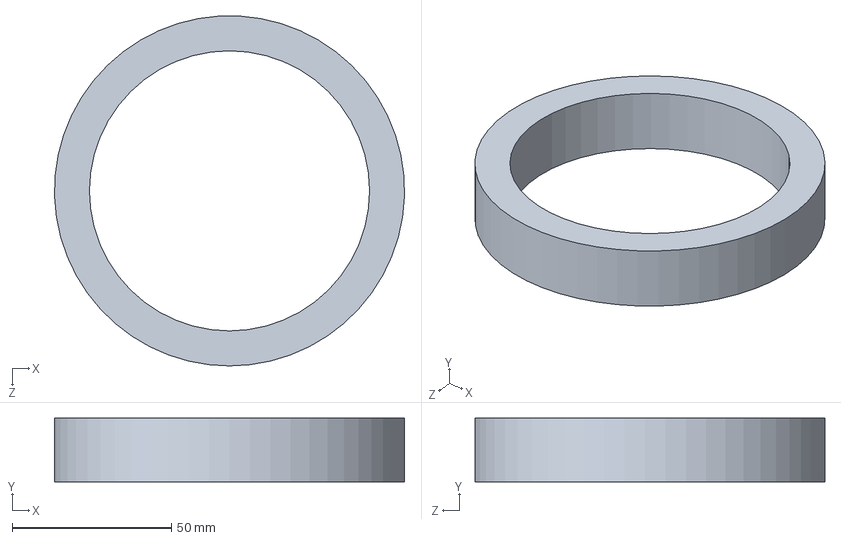
[picture p68: CAD file, 2020-11-13]
3D_models/Solidworks/下肢/機械/SHD-2SH/SHD-25-100-2SH(01-v1.0).SLDPRT
110.0 x 20.0 x 109.9 mm
