ziteh/LEAP/3D_models/Solidworks/下肢/機械/軸承(SKF單列圓柱滾子20)_内圈-01_v1.0.SLDPRT

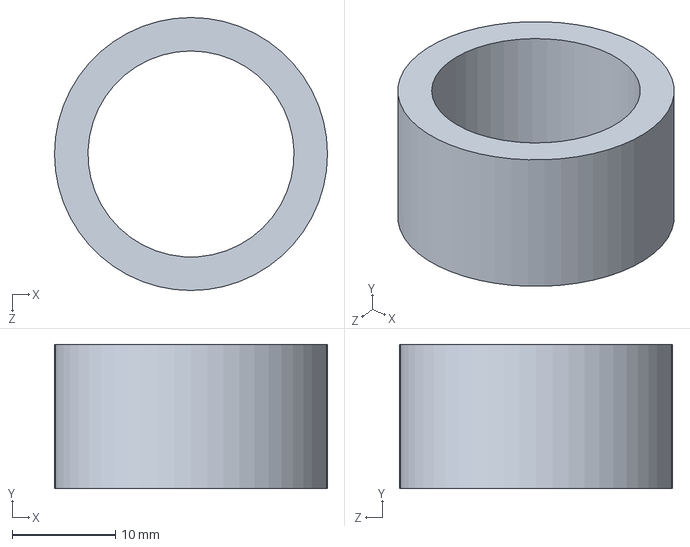
[picture p69: CAD file, 2020-11-13]
3D_models/Solidworks/下肢/機械/軸承(SKF單列圓柱滾子20)_内圈-01_v1.0.SLDPRT
26.5 x 14.0 x 26.5 mm
