ziteh/LEAP/3D_models/Solidworks/下肢/鋁擠型/3060鋁擠型(600)-01_v1.0.SLDPRT

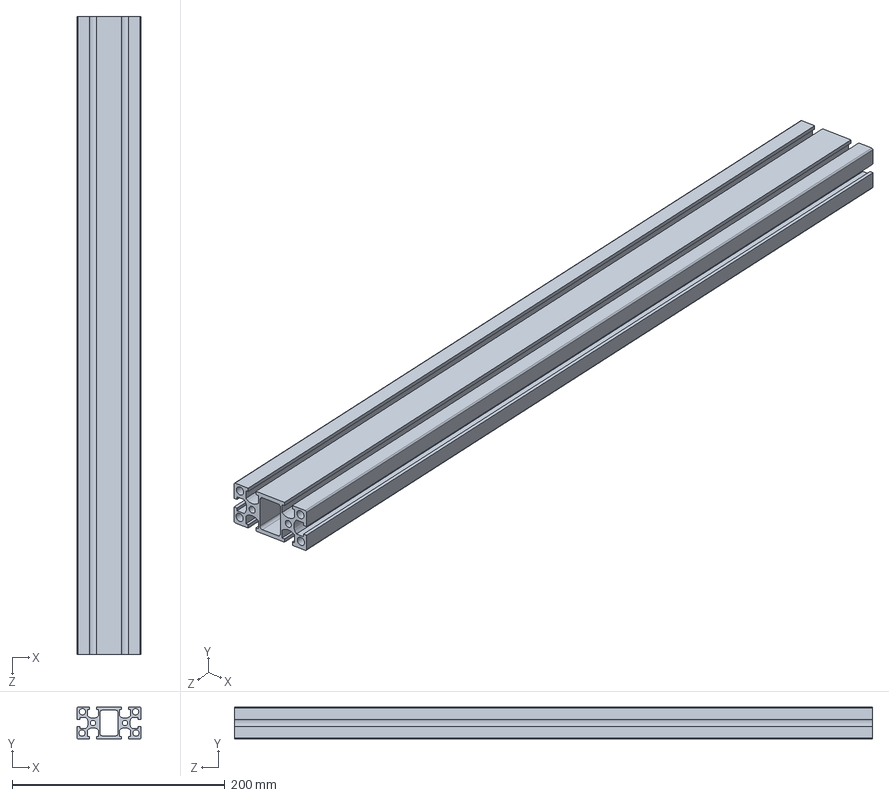
[picture p70: CAD file, 2020-11-13]
3D_models/Solidworks/下肢/鋁擠型/3060鋁擠型(600)-01_v1.0.SLDPRT
60.0 x 30.0 x 600.0 mm
