ziteh/LEAP/3D_models/Solidworks/下肢/電子電機/光遮斷器[01-v1.0].SLDPRT

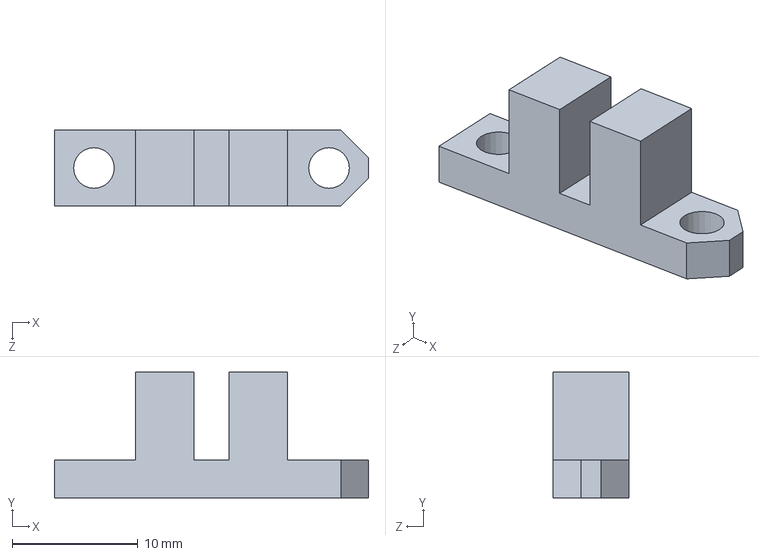
[picture p71: CAD file, 2020-11-13]
3D_models/Solidworks/下肢/電子電機/光遮斷器[01-v1.0].SLDPRT
24.9 x 10.0 x 6.00 mm
