ziteh/LEAP/3D_models/Solidworks/縮小測試用模型v2/齒輪[01-v2.0].SLDPRT

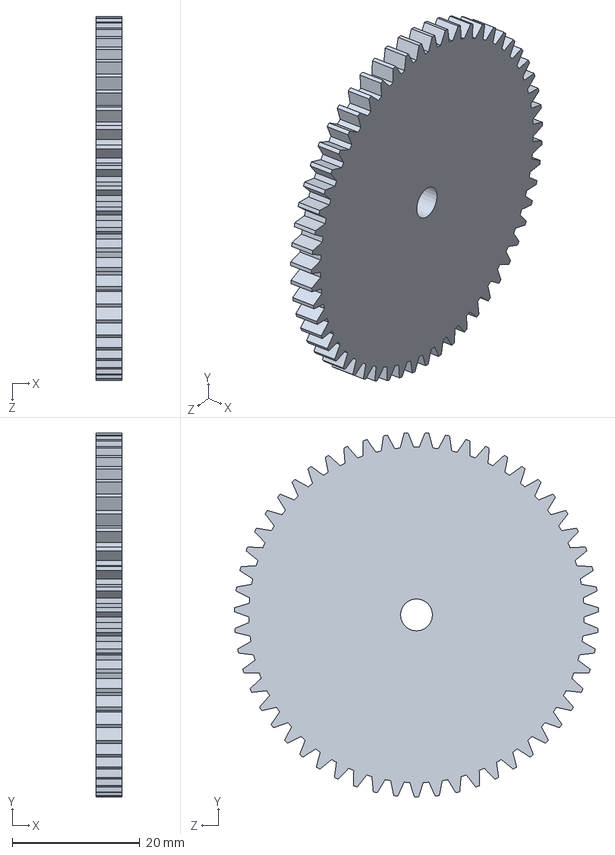
[picture p72: CAD file, 2020-11-13]
3D_models/Solidworks/縮小測試用模型v2/齒輪[01-v2.0].SLDPRT
4.00 x 57.0 x 57.0 mm
