ziteh/LEAP/3D_models/Solidworks/下肢/Others/光遮斷輪[01-v1.0].SLDPRT

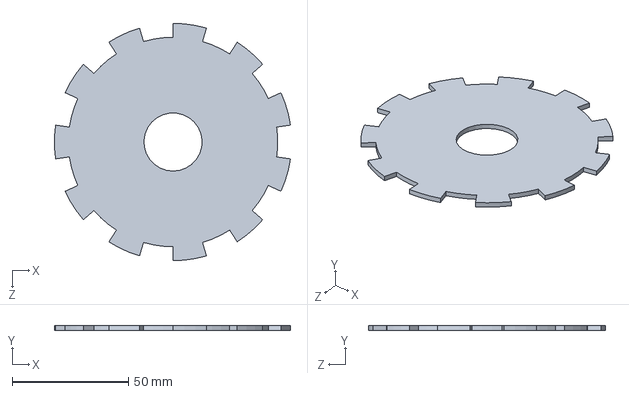
[picture p73: CAD file, 2020-11-13]
3D_models/Solidworks/下肢/Others/光遮斷輪[01-v1.0].SLDPRT
101.4 x 2.00 x 102.0 mm
