ziteh/LEAP/3D_models/Solidworks/下肢/固定/髖關節軸承軸心[01_v1.0].SLDPRT

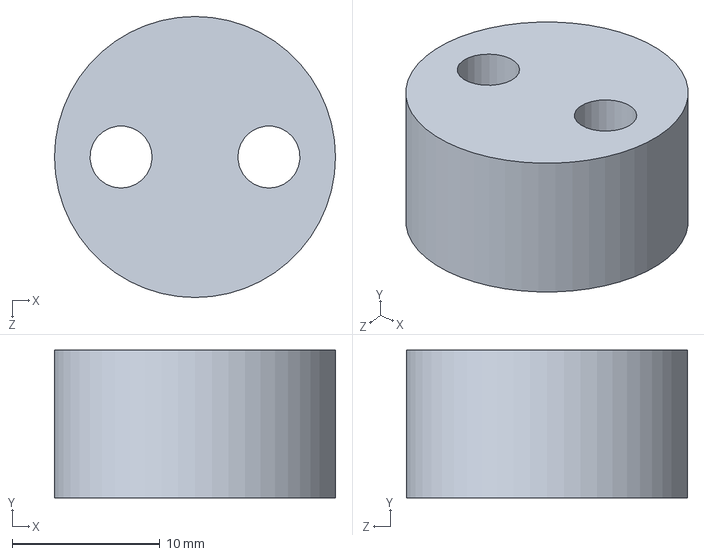
[picture p74: CAD file, 2020-11-14]
3D_models/Solidworks/下肢/固定/髖關節軸承軸心[01_v1.0].SLDPRT
19.0 x 10.0 x 19.0 mm
