ziteh/LEAP/3D_models/Solidworks/下肢/機械/SHD-2SH/shd-25-xxx-2sh.stp

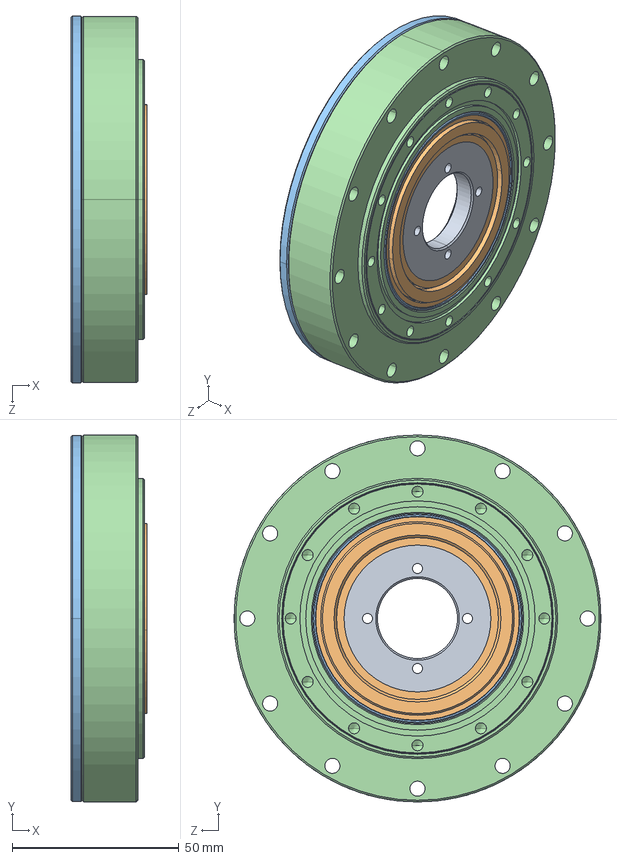
[picture p75: CAD file, 2020-11-13]
3D_models/Solidworks/下肢/機械/SHD-2SH/shd-25-xxx-2sh.stp
22.7 x 110.0 x 110.0 mm
SHD-25-2SH-WG
25 WG BEARING DS
SHD-25-2SH-FS
SHD-25-2SH-CS
