ziteh/LEAP/3D_models/Solidworks/下肢/機械/軸承(SKF單列圓柱滾子20)_外圈-01_v1.0.SLDPRT

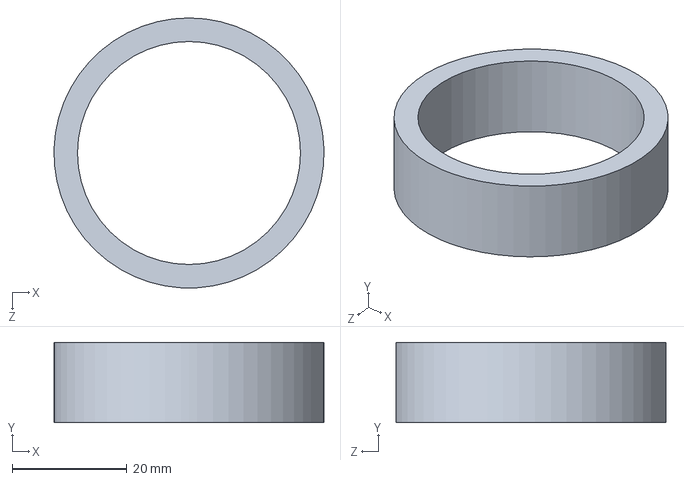
[picture p76: CAD file, 2020-11-13]
3D_models/Solidworks/下肢/機械/軸承(SKF單列圓柱滾子20)_外圈-01_v1.0.SLDPRT
47.0 x 14.0 x 47.0 mm
