ziteh/LEAP/3D_models/Solidworks/下肢/電子電機/可變電阻[01-v1.0].SLDPRT

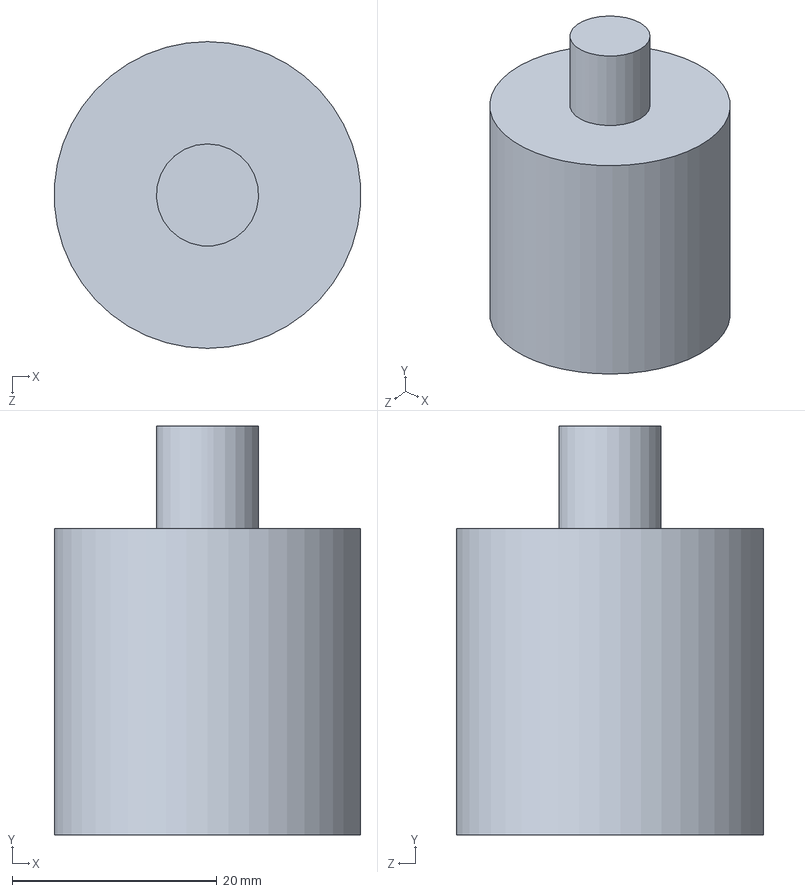
[picture p77: CAD file, 2020-11-13]
3D_models/Solidworks/下肢/電子電機/可變電阻[01-v1.0].SLDPRT
29.9 x 40.0 x 30.0 mm
