ziteh/LEAP/3D_models/Solidworks/縮小測試用模型/定位齒輪[01-v1.DXF

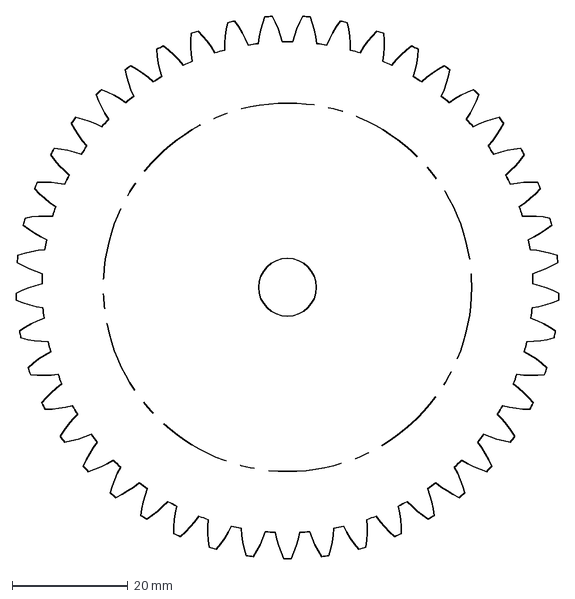
[picture p78: CAD file, 2020-11-13]
3D_models/Solidworks/縮小測試用模型/定位齒輪[01-v1.DXF
94.0 x 93.9 mm
