ziteh/LEAP/3D_models/Solidworks/下肢/機械/諧波減速機(SHF-25-100)_波產生器-01_v1.0.SLDPRT

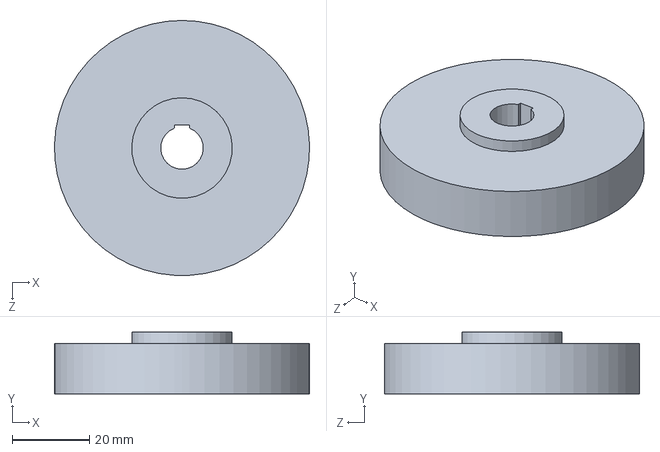
[picture p79: CAD file, 2020-11-13]
3D_models/Solidworks/下肢/機械/諧波減速機(SHF-25-100)_波產生器-01_v1.0.SLDPRT
66.0 x 16.0 x 66.0 mm
