ziteh/LEAP/3D_models/Solidworks/下肢/固定/EC90flot軸心固定塊(01_v4.0).SLDPRT

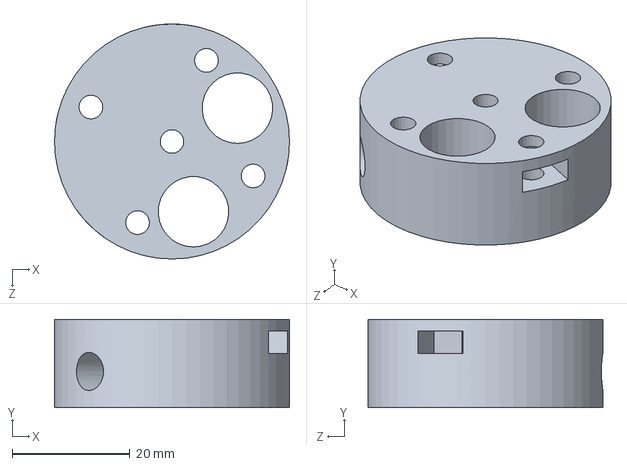
[picture p80: CAD file, 2020-11-14]
3D_models/Solidworks/下肢/固定/EC90flot軸心固定塊(01_v4.0).SLDPRT
40.0 x 15.0 x 40.0 mm
