ziteh/LEAP/3D_models/Solidworks/下肢/機械/諧波減速機(SHF-25-100)_剛性齒輪-01_v1.0.SLDPRT

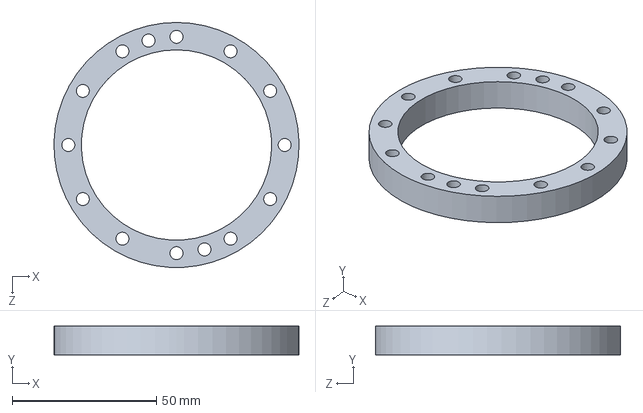
[picture p81: CAD file, 2020-11-13]
3D_models/Solidworks/下肢/機械/諧波減速機(SHF-25-100)_剛性齒輪-01_v1.0.SLDPRT
85.0 x 10.0 x 85.0 mm
