ziteh/LEAP/3D_models/Solidworks/下肢/機械/氣彈簧_缸體-01_v1.0.SLDPRT

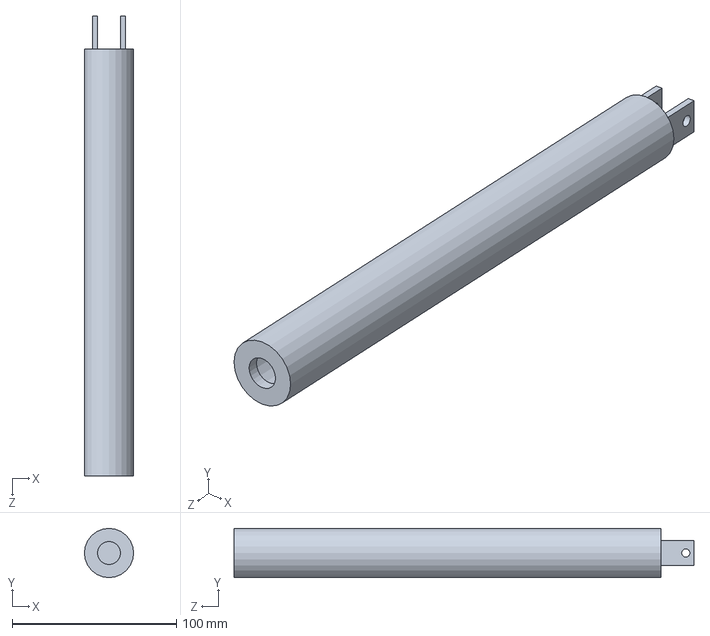
[picture p82: CAD file, 2020-11-13]
3D_models/Solidworks/下肢/機械/氣彈簧_缸體-01_v1.0.SLDPRT
30.0 x 30.0 x 280.0 mm
