ziteh/LEAP/3D_models/Solidworks/縮小測試用模型/伺服馬達SG90固定板-小腿[01-v3.0].SLDPRT

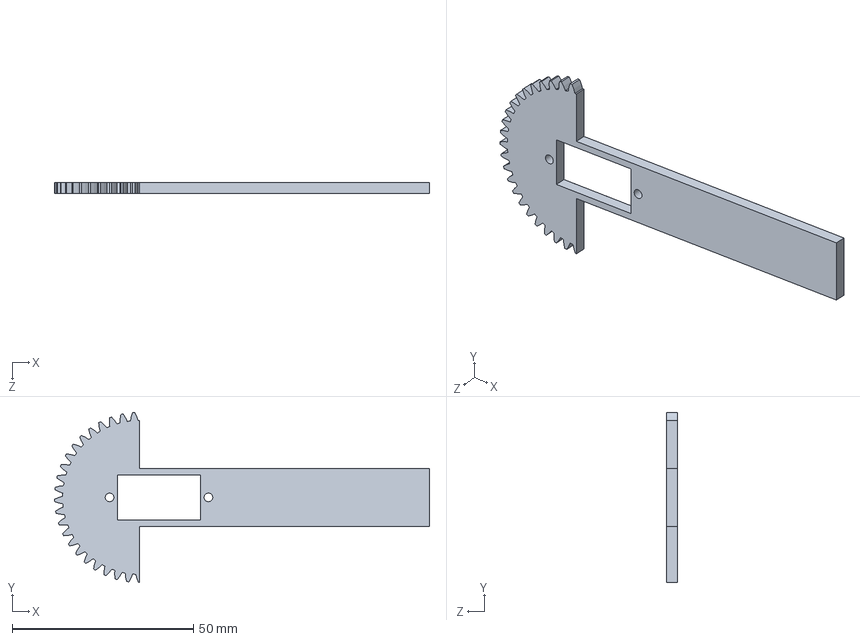
[picture p83: CAD file, 2020-11-13]
3D_models/Solidworks/縮小測試用模型/伺服馬達SG90固定板-小腿[01-v3.0].SLDPRT
103.5 x 47.0 x 3.00 mm
