ziteh/LEAP/3D_models/Solidworks/縮小測試用模型v2/3030鋁擠[01-v1.0].SLDPRT

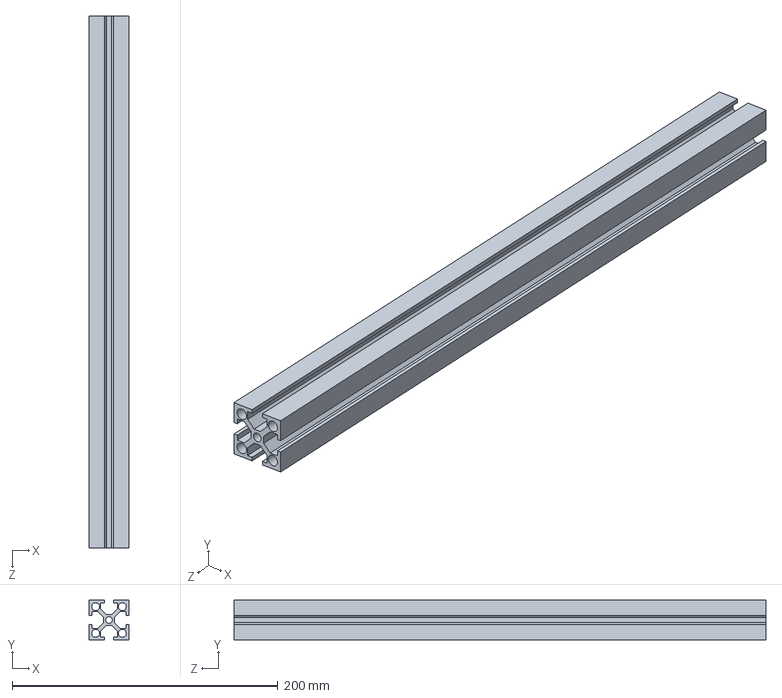
[picture p84: CAD file, 2020-11-13]
3D_models/Solidworks/縮小測試用模型v2/3030鋁擠[01-v1.0].SLDPRT
30.0 x 30.0 x 400.0 mm
