ziteh/LEAP/3D_models/Solidworks/下肢/固定/HD軸向軸承固定塊(01_v1.0).SLDPRT

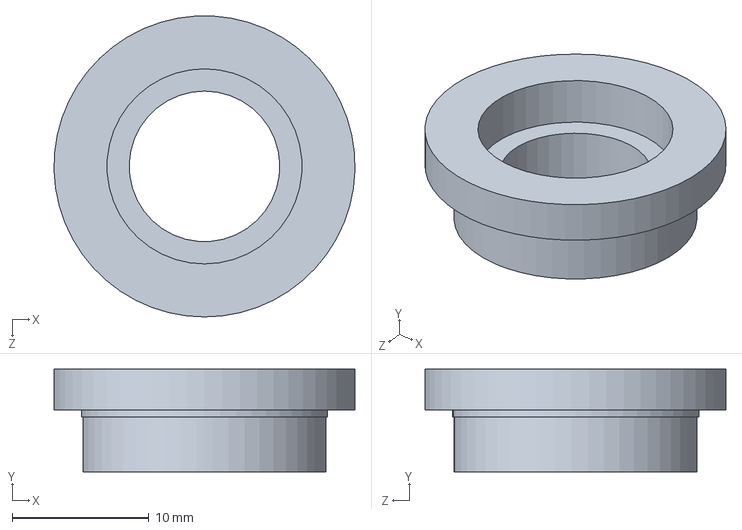
[picture p85: CAD file, 2020-11-14]
3D_models/Solidworks/下肢/固定/HD軸向軸承固定塊(01_v1.0).SLDPRT
22.0 x 7.50 x 22.0 mm
