ziteh/LEAP/3D_models/Solidworks/下肢/機械/多圈可變電阻定位齒輪組/多圈可變電阻定位齒輪組-15齒[01-v2.0].SLDPRT

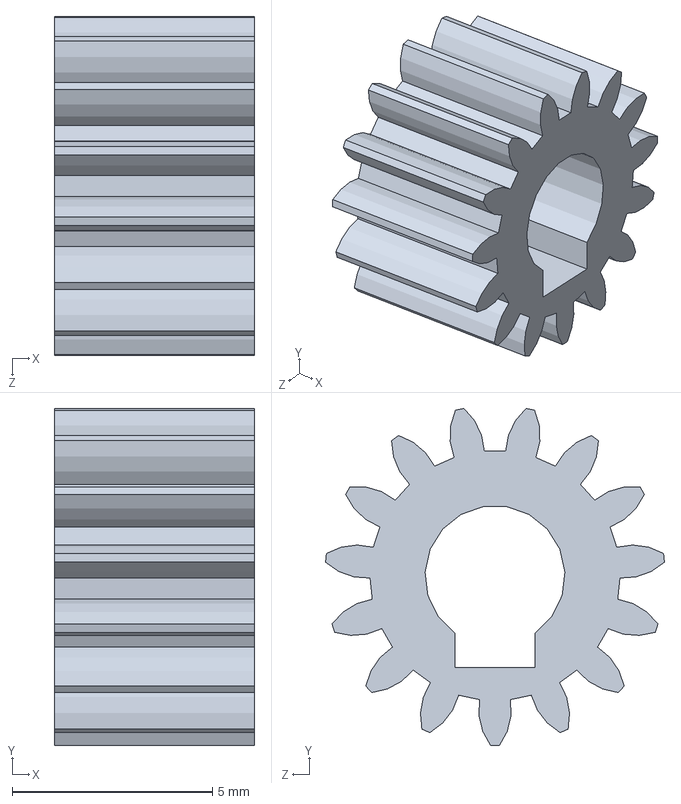
[picture p86: CAD file, 2020-11-13]
3D_models/Solidworks/下肢/機械/多圈可變電阻定位齒輪組/多圈可變電阻定位齒輪組-15齒[01-v2.0].SLDPRT
5.00 x 8.43 x 8.47 mm
