ziteh/LEAP/3D_models/Solidworks/下肢/機械/諧波減速機(SHF-25-100)_彈性齒杯-01_v1.0.SLDPRT

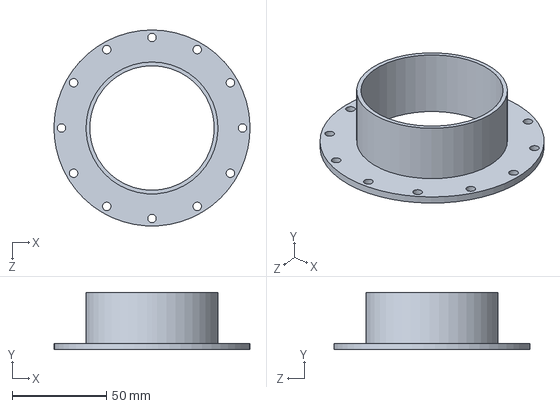
[picture p87: CAD file, 2020-11-13]
3D_models/Solidworks/下肢/機械/諧波減速機(SHF-25-100)_彈性齒杯-01_v1.0.SLDPRT
104.0 x 30.3 x 104.0 mm
