ziteh/LEAP/3D_models/Solidworks/縮小測試用模型/伺服馬達SG90用轉軸片[01-v1.0].SLDPRT

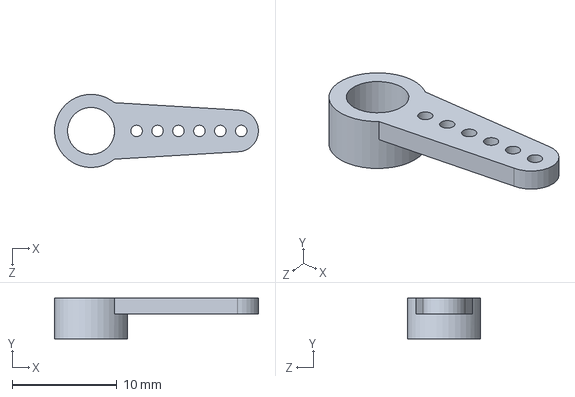
[picture p88: CAD file, 2020-11-13]
3D_models/Solidworks/縮小測試用模型/伺服馬達SG90用轉軸片[01-v1.0].SLDPRT
19.5 x 3.90 x 6.99 mm
