ziteh/LEAP/3D_models/Solidworks/下肢/固定/大腿固定片[01_v1.0].SLDPRT

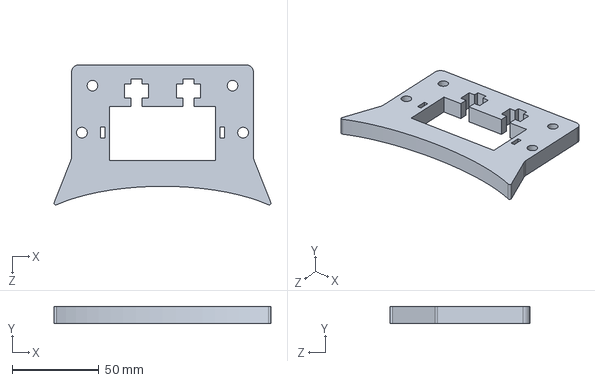
[picture p89: CAD file, 2020-11-14]
3D_models/Solidworks/下肢/固定/大腿固定片[01_v1.0].SLDPRT
125.2 x 10.0 x 80.8 mm
