ziteh/LEAP/3D_models/Solidworks/下肢/機械/多圈可變電阻定位齒輪組/多圈可變電阻定位齒輪組-m0.5 220齒[01-v1.0].SLDPRT

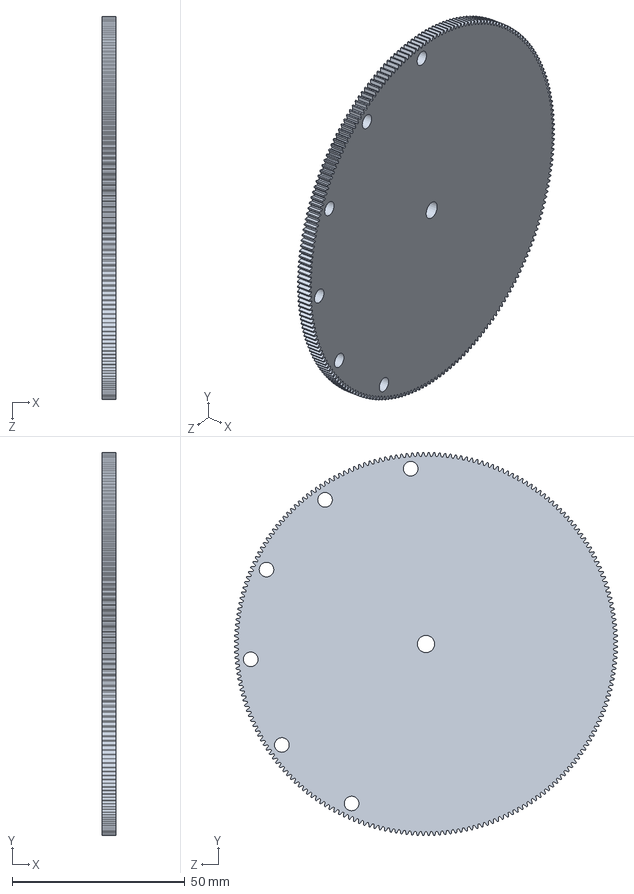
[picture p90: CAD file, 2020-11-13]
3D_models/Solidworks/下肢/機械/多圈可變電阻定位齒輪組/多圈可變電阻定位齒輪組-m0.5 220齒[01-v1.0].SLDPRT
4.00 x 111.0 x 111.0 mm
