ziteh/LEAP/3D_models/Solidworks/下肢/機械/氣彈簧_伸縮杆-01_v1.0.SLDPRT

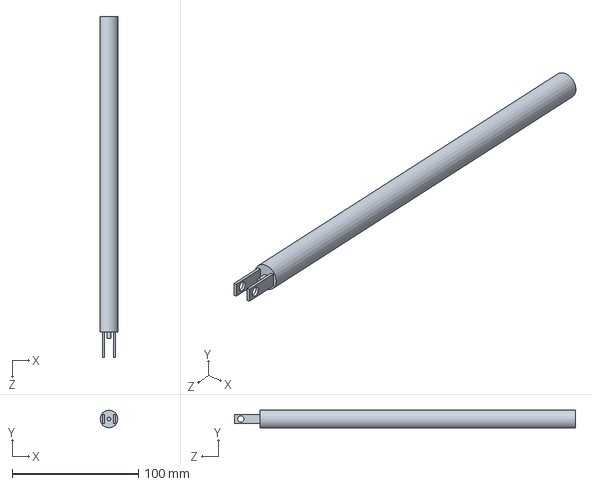
[picture p91: CAD file, 2020-11-13]
3D_models/Solidworks/下肢/機械/氣彈簧_伸縮杆-01_v1.0.SLDPRT
14.0 x 14.0 x 270.0 mm
