ziteh/LEAP/3D_models/Solidworks/縮小測試用模型/可變電阻固定套[01-v1.0].SLDPRT

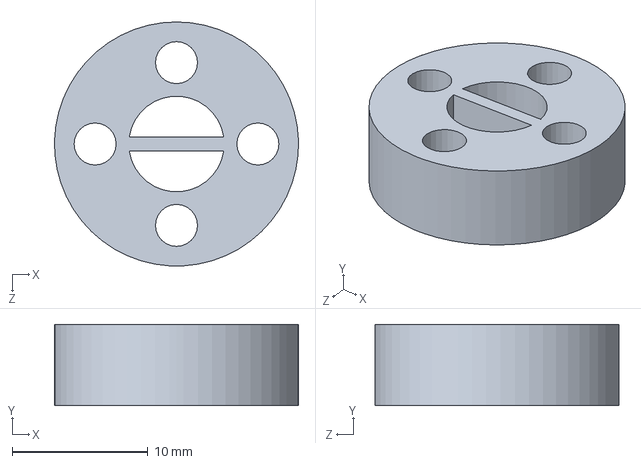
[picture p92: CAD file, 2020-11-13]
3D_models/Solidworks/縮小測試用模型/可變電阻固定套[01-v1.0].SLDPRT
18.0 x 6.00 x 18.0 mm
