ziteh/LEAP/3D_models/Solidworks/縮小測試用模型v2/齒輪[02-v1.2.2].SLDPRT

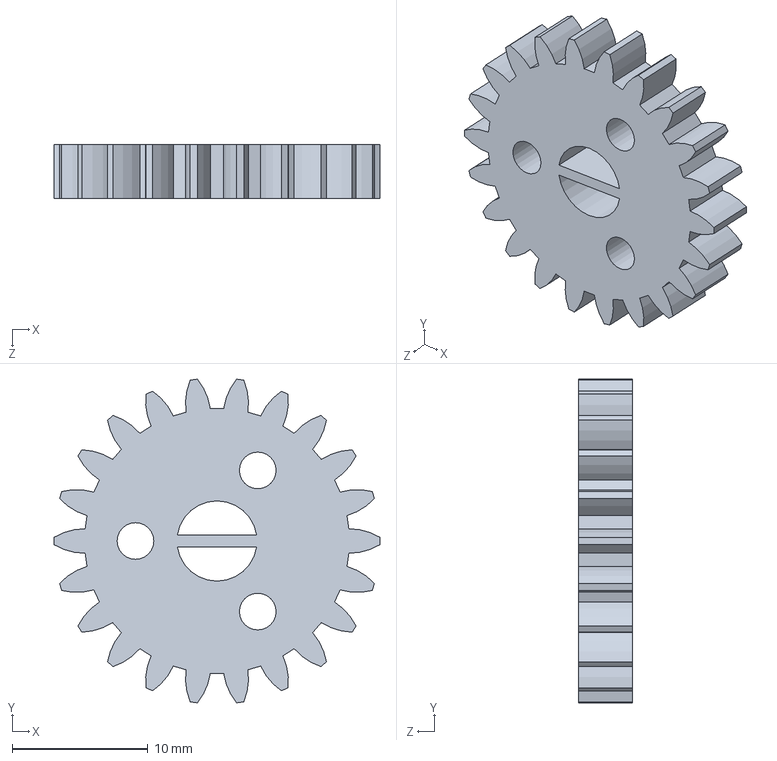
[picture p93: CAD file, 2020-11-13]
3D_models/Solidworks/縮小測試用模型v2/齒輪[02-v1.2.2].SLDPRT
24.0 x 23.8 x 4.00 mm
