ziteh/LEAP/3D_models/Solidworks/下肢/固定/SHD-2SH_彈性齒杯固定片(01_v4.2).SLDPRT

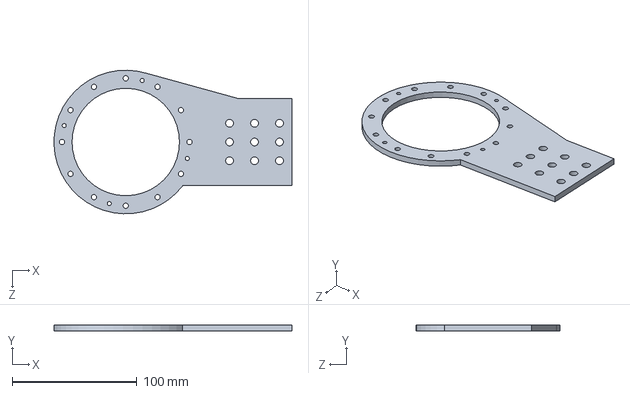
[picture p95: CAD file, 2020-11-14]
3D_models/Solidworks/下肢/固定/SHD-2SH_彈性齒杯固定片(01_v4.2).SLDPRT
190.6 x 4.50 x 114.9 mm
