ziteh/LEAP/3D_models/Solidworks/縮小測試用模型/可變電阻齒輪[01-v2.0].SLDPRT

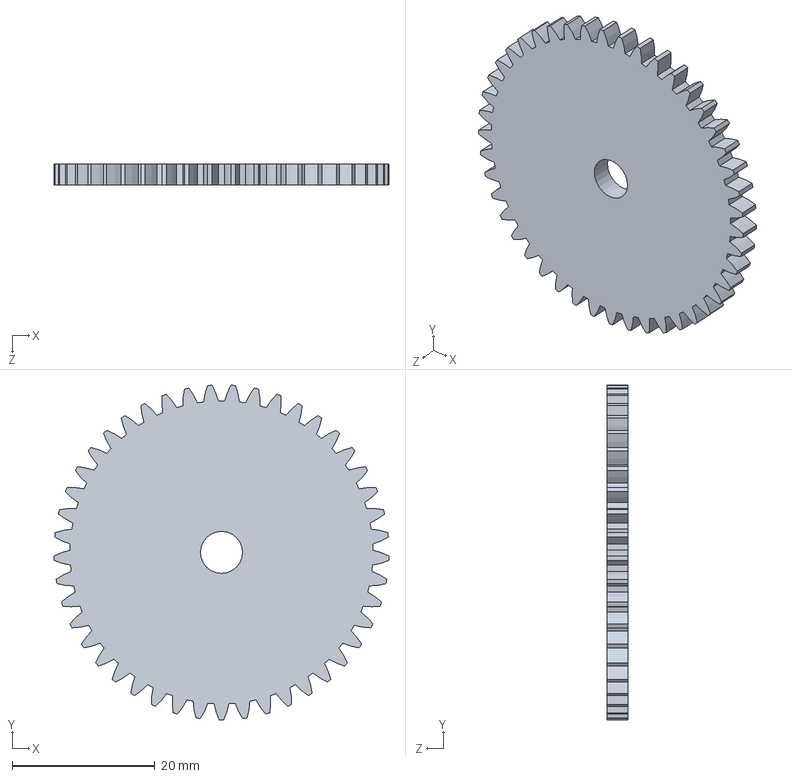
[picture p96: CAD file, 2020-11-13]
3D_models/Solidworks/縮小測試用模型/可變電阻齒輪[01-v2.0].SLDPRT
47.0 x 47.0 x 3.00 mm
