ziteh/LEAP/3D_models/Solidworks/縮小測試用模型v2/齒輪[01-v1.DXF

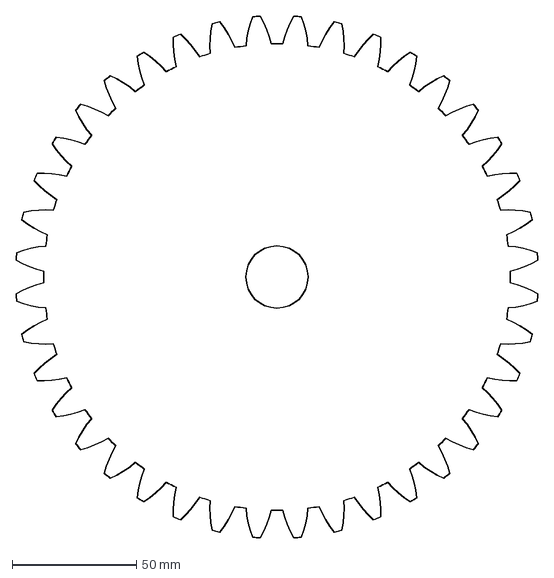
[picture p97: CAD file, 2020-11-13]
3D_models/Solidworks/縮小測試用模型v2/齒輪[01-v1.DXF
209.6 x 209.6 mm
