ziteh/LEAP/3D_models/Solidworks/縮小測試用模型/伺服馬達SG90-extender_30mm[01-v2.0].SLDPRT

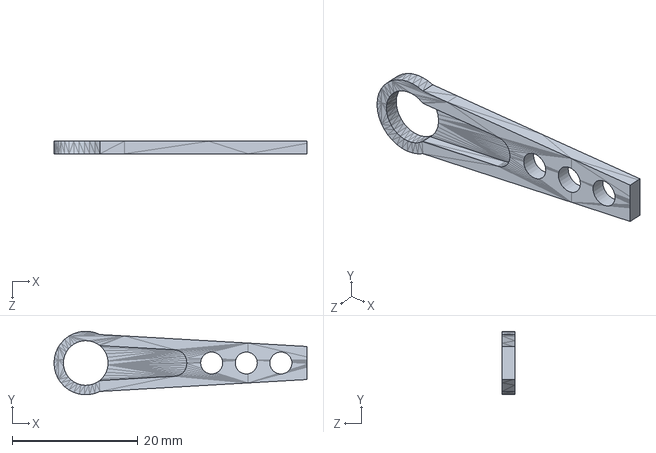
[picture p99: CAD file, 2020-11-13]
3D_models/Solidworks/縮小測試用模型/伺服馬達SG90-extender_30mm[01-v2.0].SLDPRT
40.2 x 10.1 x 2.00 mm
