ziteh/LEAP/3D_models/Solidworks/下肢/固定/SHD-2SH_剛性齒輪固定片(01_v2.1).SLDPRT

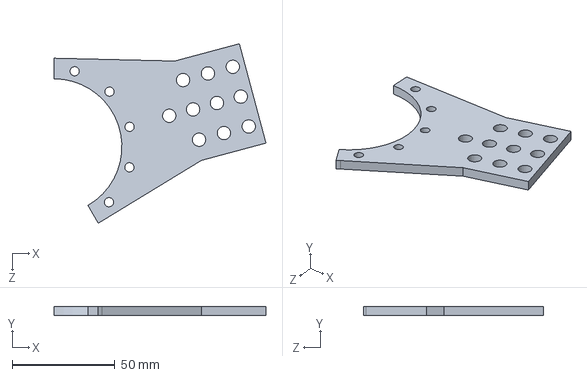
[picture p100: CAD file, 2020-11-14]
3D_models/Solidworks/下肢/固定/SHD-2SH_剛性齒輪固定片(01_v2.1).SLDPRT
103.1 x 4.50 x 87.3 mm
