ziteh/LEAP/3D_models/Solidworks/縮小測試用模型/伺服馬達SG90用轉軸片壓克力套[01-v1.0].SLDPRT

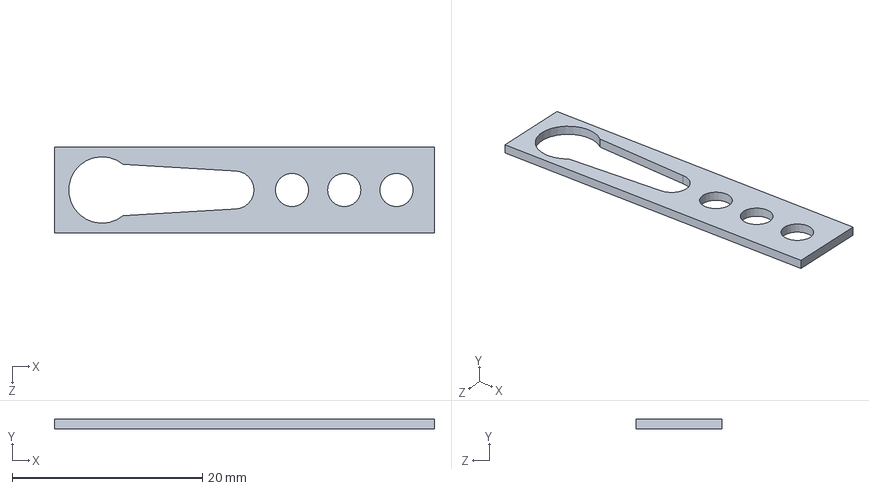
[picture p101: CAD file, 2020-11-13]
3D_models/Solidworks/縮小測試用模型/伺服馬達SG90用轉軸片壓克力套[01-v1.0].SLDPRT
40.0 x 1.00 x 9.00 mm
