ziteh/LEAP/3D_models/Solidworks/縮小測試用模型v2/MG996R[01-v1.0].SLDPRT

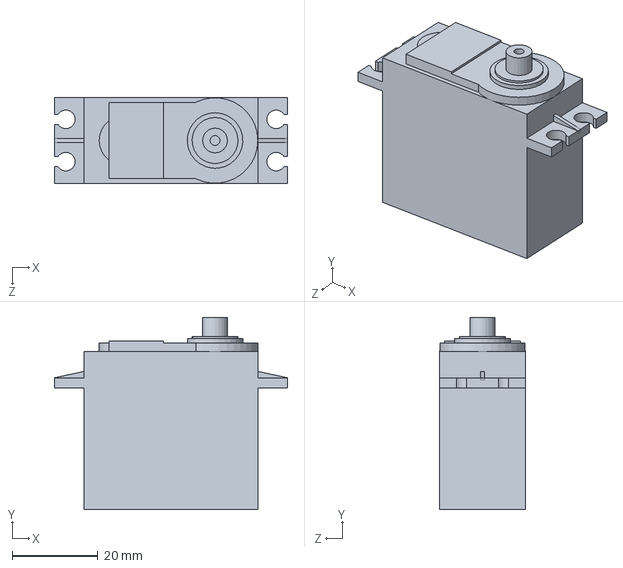
[picture p102: CAD file, 2020-11-13]
3D_models/Solidworks/縮小測試用模型v2/MG996R[01-v1.0].SLDPRT
54.5 x 45.0 x 20.0 mm
