ziteh/LEAP/3D_models/Solidworks/下肢/固定/定位多圈可變電阻固定片[02_v5.0].SLDPRT

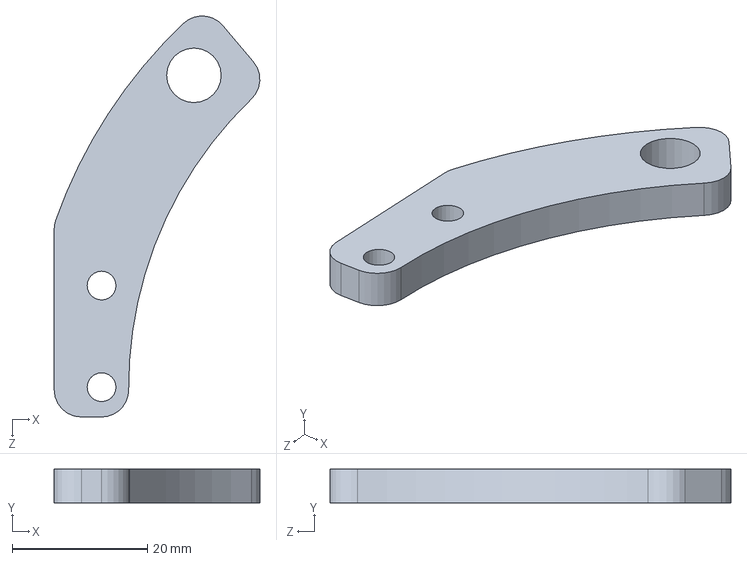
[picture p103: CAD file, 2020-11-14]
3D_models/Solidworks/下肢/固定/定位多圈可變電阻固定片[02_v5.0].SLDPRT
30.4 x 5.00 x 59.2 mm
