ziteh/LEAP/3D_models/Solidworks/縮小測試用模型v2/小腿板[01-v1.0].SLDPRT

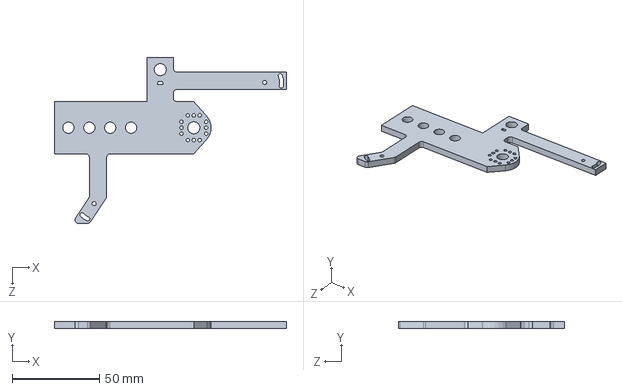
[picture p104: CAD file, 2020-11-13]
3D_models/Solidworks/縮小測試用模型v2/小腿板[01-v1.0].SLDPRT
133.2 x 4.00 x 95.3 mm
