ziteh/LEAP/3D_models/Solidworks/下肢/固定/FSR固定片[02_v4.0].SLDPRT

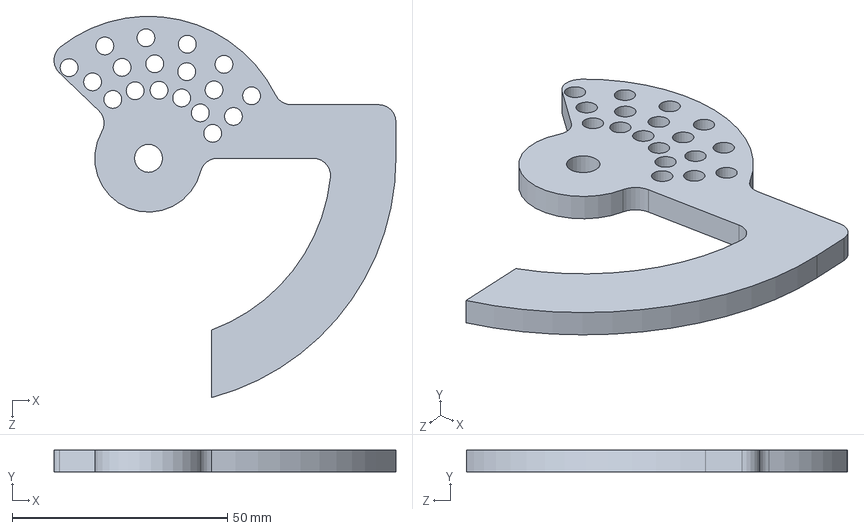
[picture p105: CAD file, 2020-11-14]
3D_models/Solidworks/下肢/固定/FSR固定片[02_v4.0].SLDPRT
79.5 x 5.00 x 88.6 mm
