ziteh/LEAP/3D_models/Solidworks/下肢/固定/腿部綁帶固定片[01_v1.0].SLDPRT

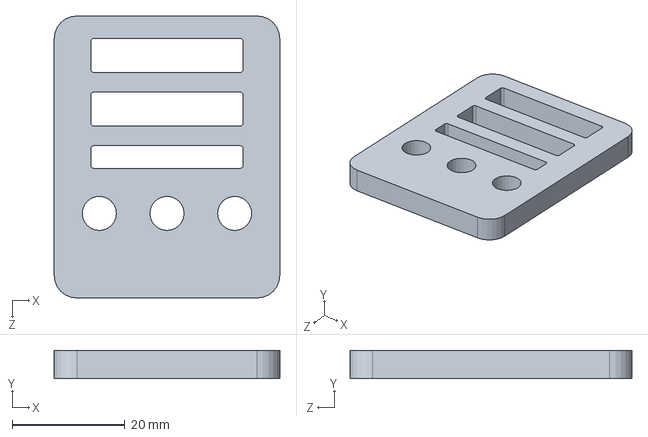
[picture p106: CAD file, 2020-11-14]
3D_models/Solidworks/下肢/固定/腿部綁帶固定片[01_v1.0].SLDPRT
40.0 x 5.00 x 50.0 mm
