ziteh/LEAP/3D_models/Solidworks/下肢/固定/小腿固定片[02_v2.0].SLDPRT

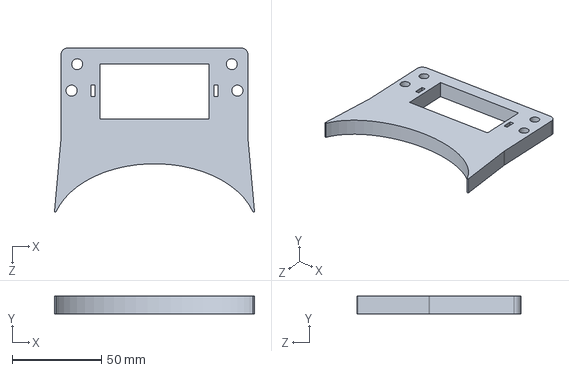
[picture p108: CAD file, 2020-11-14]
3D_models/Solidworks/下肢/固定/小腿固定片[02_v2.0].SLDPRT
112.2 x 10.0 x 92.1 mm
