ziteh/LEAP/3D_models/Solidworks/下肢/固定/SHD-2SH_彈性齒杯-可變電阻齒輪固定片[02_v2.0].SLDPRT

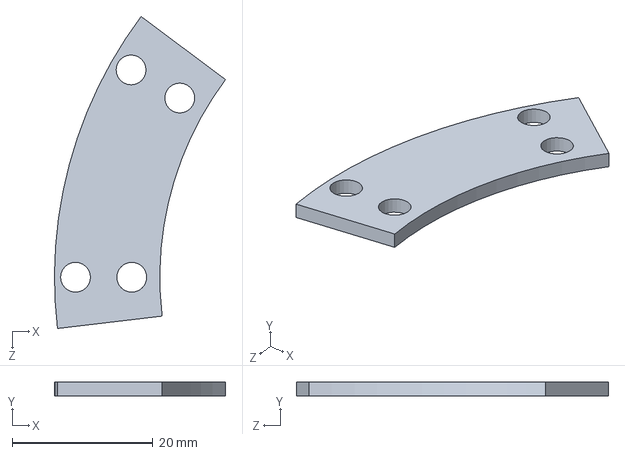
[picture p109: CAD file, 2020-11-14]
3D_models/Solidworks/下肢/固定/SHD-2SH_彈性齒杯-可變電阻齒輪固定片[02_v2.0].SLDPRT
24.3 x 2.00 x 44.4 mm
