ziteh/LEAP/3D_models/Solidworks/下肢/固定/微動開關(SS-5GL)固定片[02_v2.0].SLDPRT

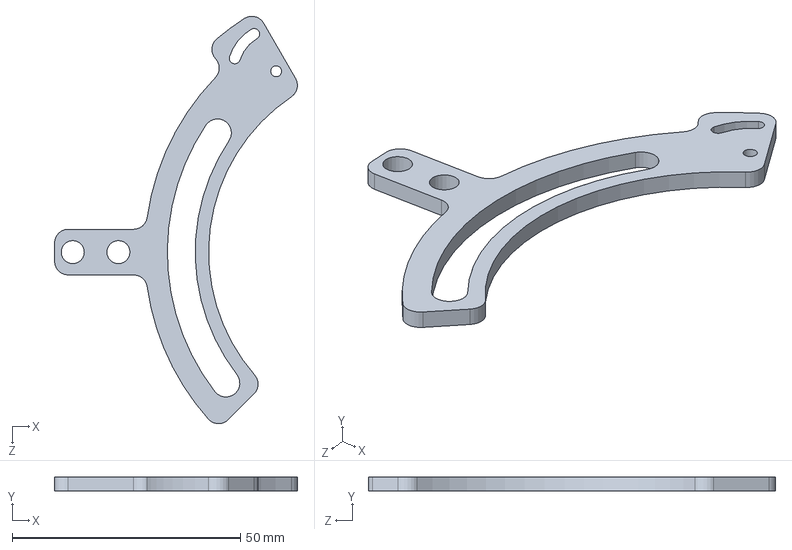
[picture p111: CAD file, 2020-11-14]
3D_models/Solidworks/下肢/固定/微動開關(SS-5GL)固定片[02_v2.0].SLDPRT
53.2 x 3.00 x 89.2 mm
