ziteh/LEAP/3D_models/Solidworks/下肢/固定/腳踝軸承軸心固定塊[01_v1.0].SLDPRT

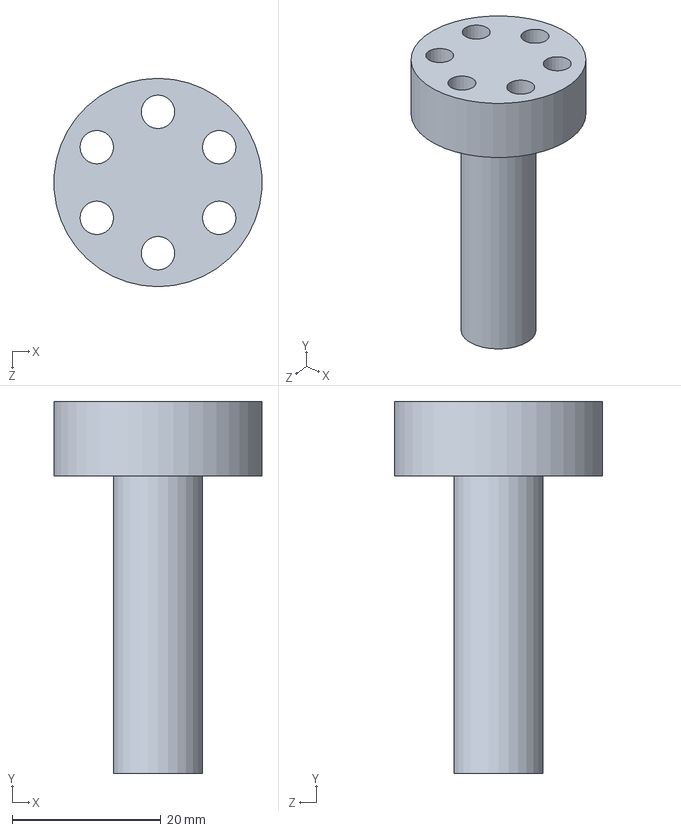
[picture p112: CAD file, 2020-11-13]
3D_models/Solidworks/下肢/固定/腳踝軸承軸心固定塊[01_v1.0].SLDPRT
27.9 x 50.0 x 28.0 mm
