ziteh/LEAP/3D_models/Solidworks/下肢/固定/腳底板螺帽固定片[01_v1.0].SLDPRT

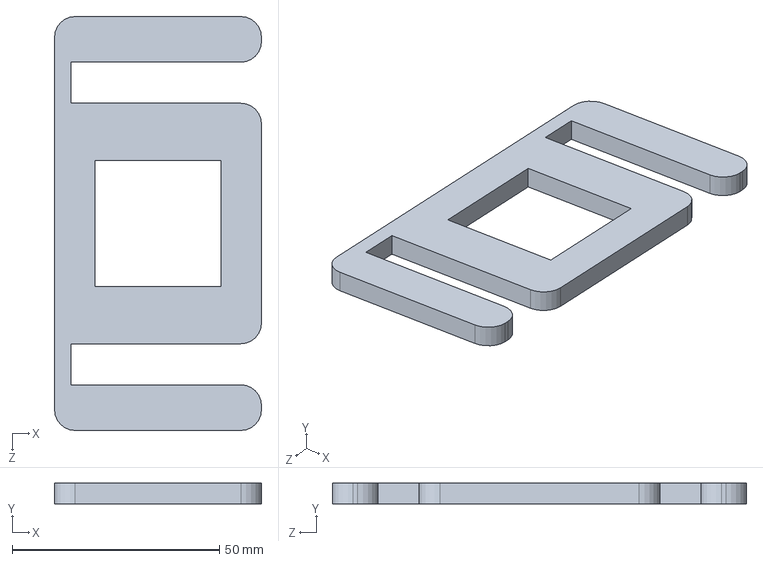
[picture p113: CAD file, 2020-11-13]
3D_models/Solidworks/下肢/固定/腳底板螺帽固定片[01_v1.0].SLDPRT
50.0 x 5.00 x 100.0 mm
