ziteh/LEAP/3D_models/Solidworks/下肢/固定/EC90flot固定片(02_v3.1).SLDPRT

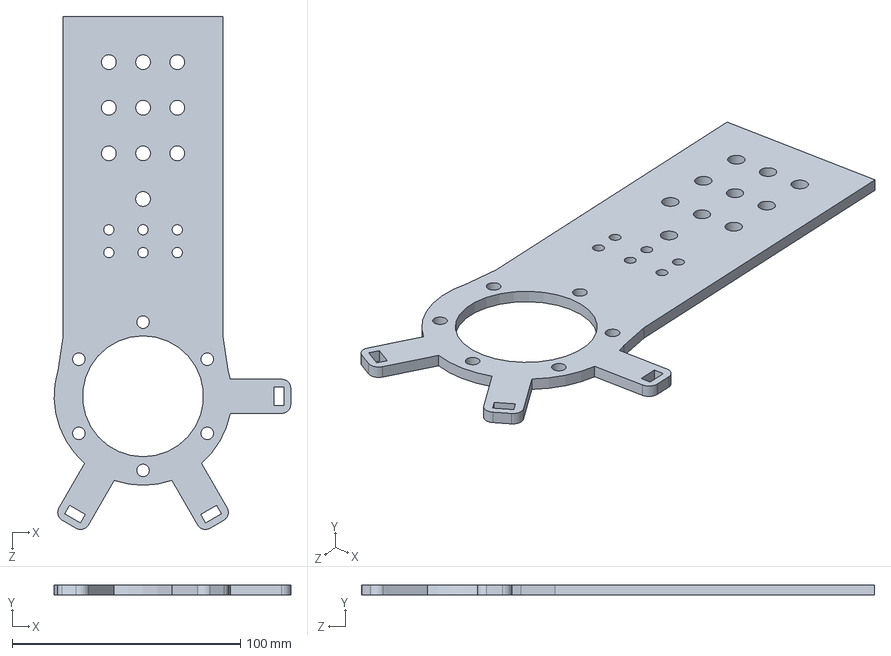
[picture p114: CAD file, 2020-11-13]
3D_models/Solidworks/下肢/固定/EC90flot固定片(02_v3.1).SLDPRT
103.8 x 4.50 x 224.9 mm
