ziteh/LEAP/3D_models/Solidworks/下肢/固定/軸承固定座-KFL12固定片[01-v1.0].SLDPRT

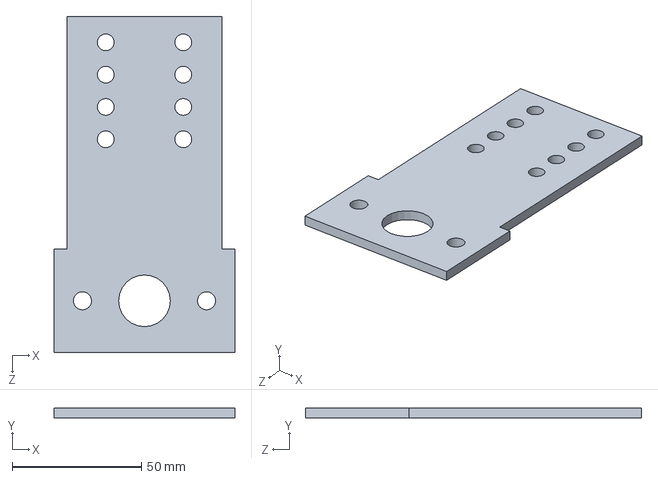
[picture p116: CAD file, 2020-11-13]
3D_models/Solidworks/下肢/固定/軸承固定座-KFL12固定片[01-v1.0].SLDPRT
70.0 x 4.00 x 130.0 mm
