ziteh/LEAP/3D_models/Solidworks/下肢/固定/定位多圈可變電阻固定片[01_v5.0].SLDPRT

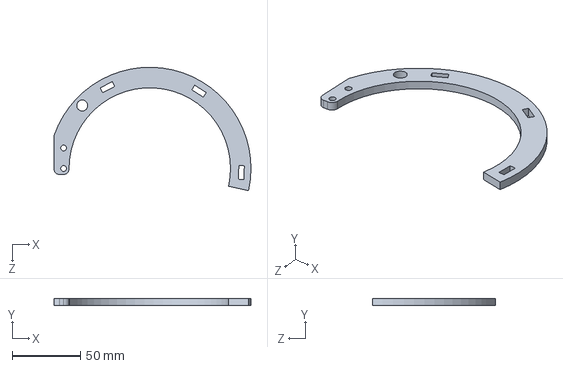
[picture p117: CAD file, 2020-11-13]
3D_models/Solidworks/下肢/固定/定位多圈可變電阻固定片[01_v5.0].SLDPRT
144.0 x 5.00 x 90.2 mm
