ziteh/LEAP/3D_models/Solidworks/下肢/固定/腳底板固定塊[01_v1.0].SLDPRT

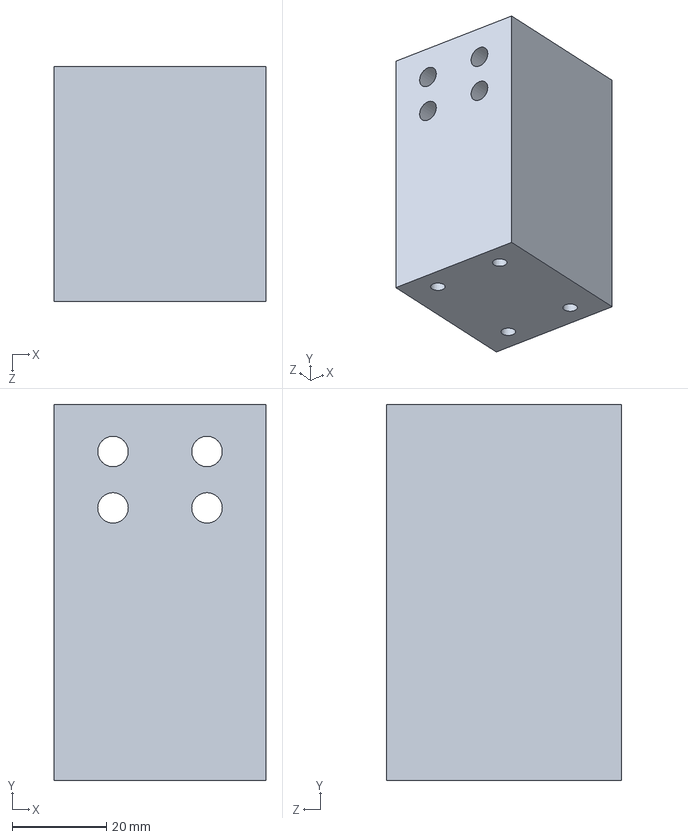
[picture p118: CAD file, 2020-11-13]
3D_models/Solidworks/下肢/固定/腳底板固定塊[01_v1.0].SLDPRT
45.0 x 80.0 x 50.0 mm
