ziteh/LEAP/3D_models/Solidworks/下肢/固定/氣彈簧固定架-01_v2.0.SLDPRT

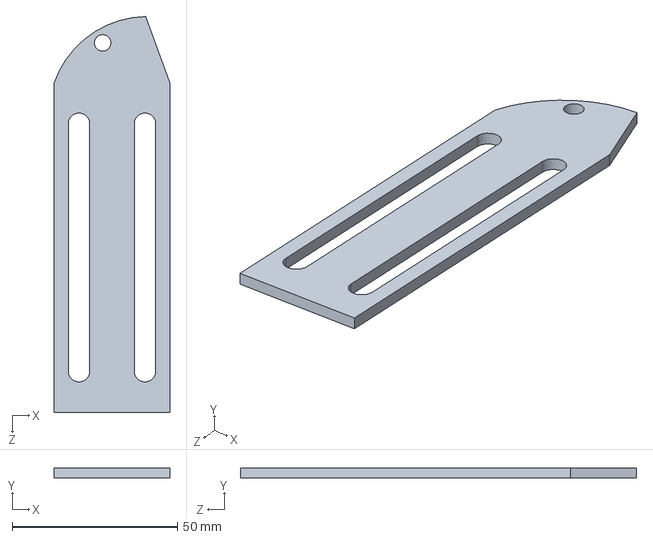
[picture p119: CAD file, 2020-11-13]
3D_models/Solidworks/下肢/固定/氣彈簧固定架-01_v2.0.SLDPRT
35.0 x 3.00 x 120.0 mm
