ziteh/LEAP/3D_models/Solidworks/下肢/固定/腳底板側邊三角固定片[01_v1.0].SLDPRT

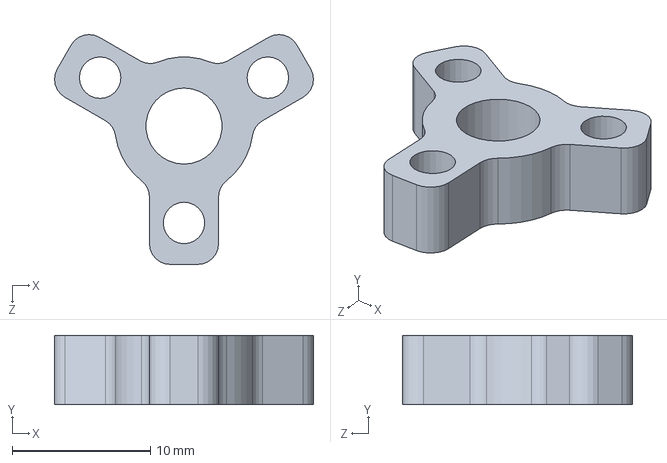
[picture p120: CAD file, 2020-11-13]
3D_models/Solidworks/下肢/固定/腳底板側邊三角固定片[01_v1.0].SLDPRT
18.7 x 5.00 x 16.6 mm
