ziteh/LEAP/3D_models/Solidworks/下肢/固定/微動開關(SS-5GL)固定片[01_v3.0].SLDPRT

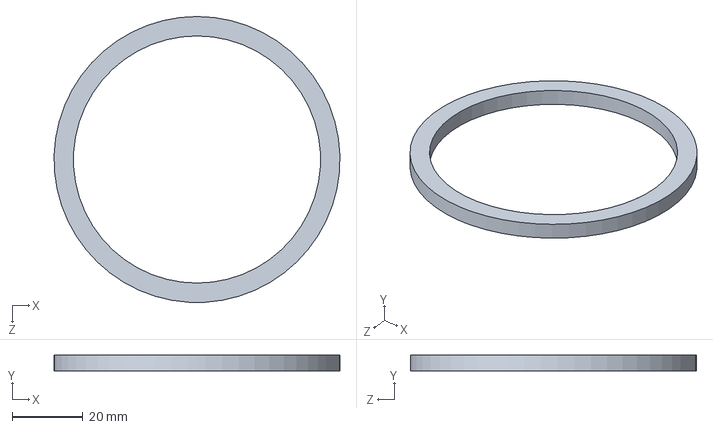
[picture p121: CAD file, 2020-11-13]
3D_models/Solidworks/下肢/固定/微動開關(SS-5GL)固定片[01_v3.0].SLDPRT
81.0 x 4.50 x 81.0 mm
