ziteh/LEAP/3D_models/Solidworks/下肢/固定/腳踝軸承軸心固定片[01_v1.0].SLDPRT

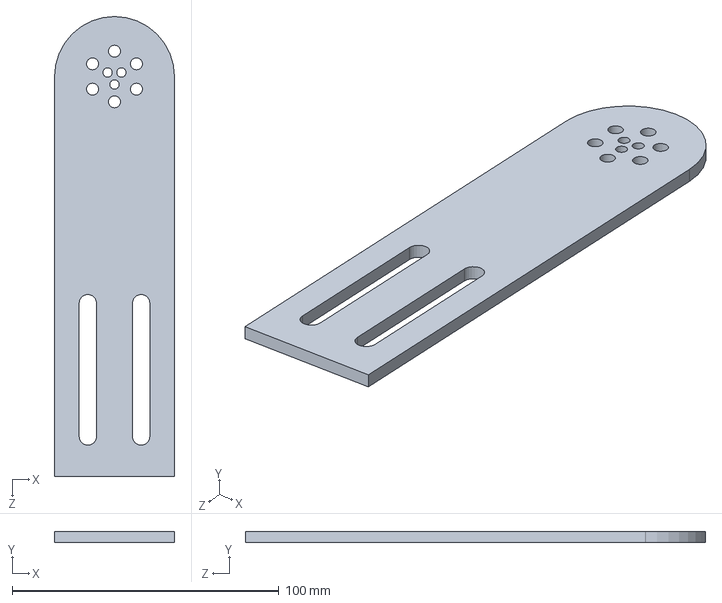
[picture p122: CAD file, 2020-11-13]
3D_models/Solidworks/下肢/固定/腳踝軸承軸心固定片[01_v1.0].SLDPRT
45.0 x 4.00 x 172.5 mm
