ziteh/LEAP/3D_models/Solidworks/下肢/固定/定位多圈可變電阻固定塊[01_v1.0].SLDPRT

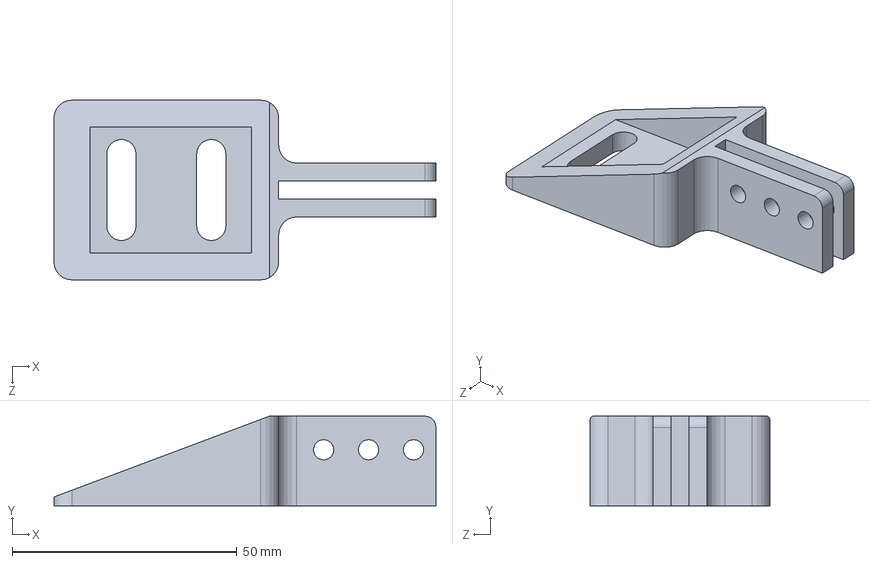
[picture p123: CAD file, 2020-11-13]
3D_models/Solidworks/下肢/固定/定位多圈可變電阻固定塊[01_v1.0].SLDPRT
85.0 x 20.0 x 40.0 mm
