ziteh/LEAP/3D_models/Solidworks/下肢/固定/腳底板前側固定片[01_v1.0].SLDPRT

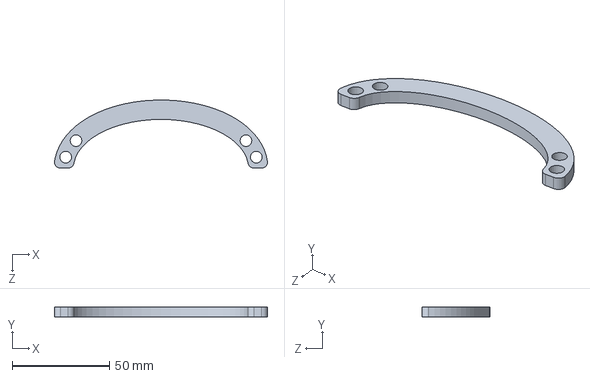
[picture p124: CAD file, 2020-11-13]
3D_models/Solidworks/下肢/固定/腳底板前側固定片[01_v1.0].SLDPRT
109.5 x 5.00 x 35.0 mm
