ziteh/LEAP/3D_models/Solidworks/下肢/固定/軸承固定座(外圈47)-01_v1.0.SLDPRT

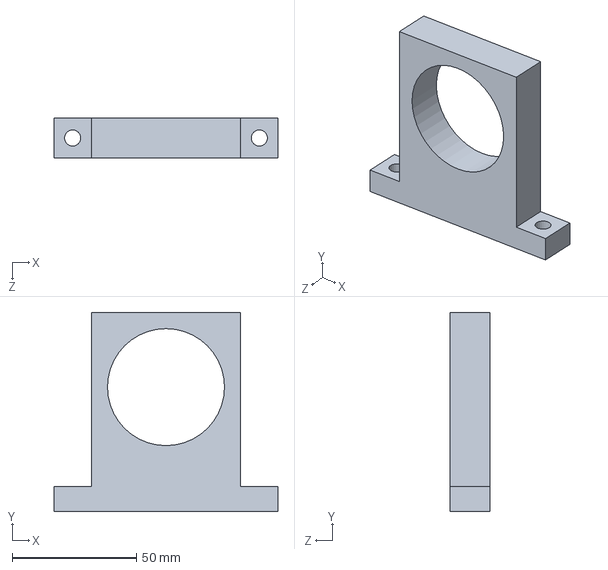
[picture p125: CAD file, 2020-11-13]
3D_models/Solidworks/下肢/固定/軸承固定座(外圈47)-01_v1.0.SLDPRT
90.0 x 80.0 x 16.0 mm
