ziteh/LEAP/3D_models/Solidworks/下肢/固定/軸固定座(内圈20)-01_v1.0.SLDPRT

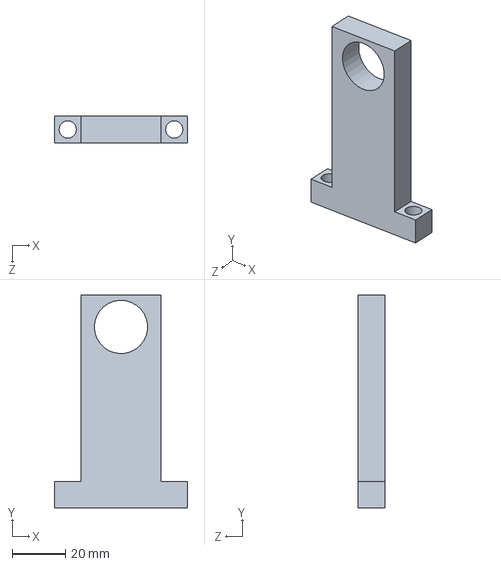
[picture p126: CAD file, 2020-11-13]
3D_models/Solidworks/下肢/固定/軸固定座(内圈20)-01_v1.0.SLDPRT
50.0 x 80.0 x 10.0 mm
