ziteh/LEAP/3D_models/Solidworks/下肢/固定/微動開關固定片[01_v1.0].SLDPRT

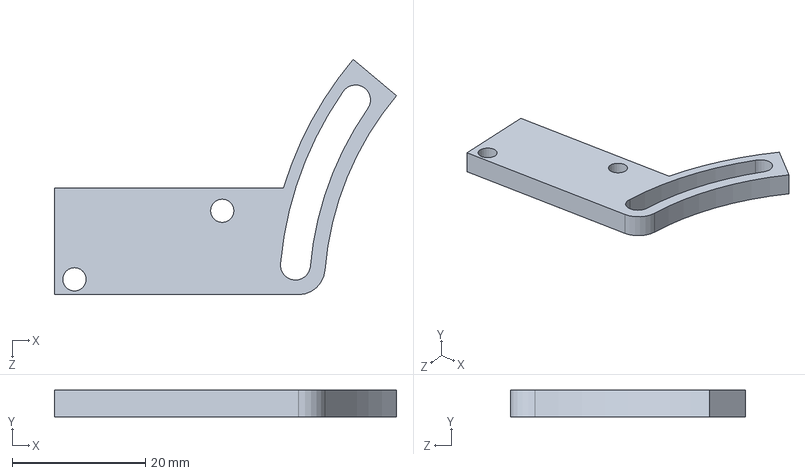
[picture p127: CAD file, 2020-11-13]
3D_models/Solidworks/下肢/固定/微動開關固定片[01_v1.0].SLDPRT
51.4 x 4.00 x 35.4 mm
