ziteh/LEAP/3D_models/Solidworks/下肢/固定/光遮斷器固定片[01_v1.0].SLDPRT

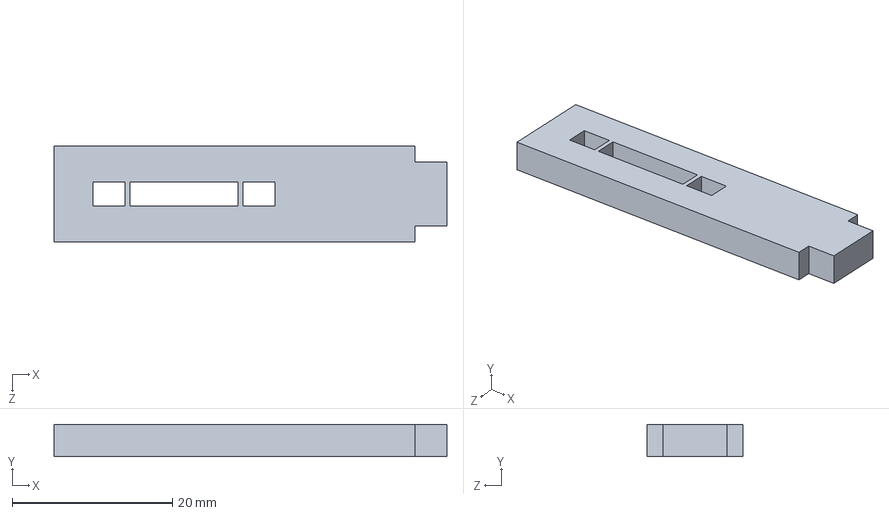
[picture p128: CAD file, 2020-11-13]
3D_models/Solidworks/下肢/固定/光遮斷器固定片[01_v1.0].SLDPRT
49.0 x 4.00 x 12.0 mm
