ziteh/LEAP/3D_models/Solidworks/下肢/固定/SHD-2SH_剛性齒輪-編碼器齒輪連接固定片(01_v1.0).SLDPRT

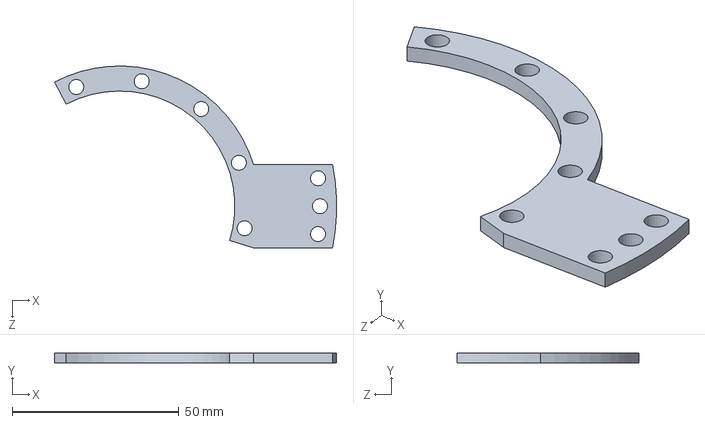
[picture p129: CAD file, 2020-11-13]
3D_models/Solidworks/下肢/固定/SHD-2SH_剛性齒輪-編碼器齒輪連接固定片(01_v1.0).SLDPRT
84.5 x 3.00 x 54.5 mm
