ziteh/LEAP/3D_models/Solidworks/下肢/固定/腰部綁帶固定片[01_v1.0].SLDPRT

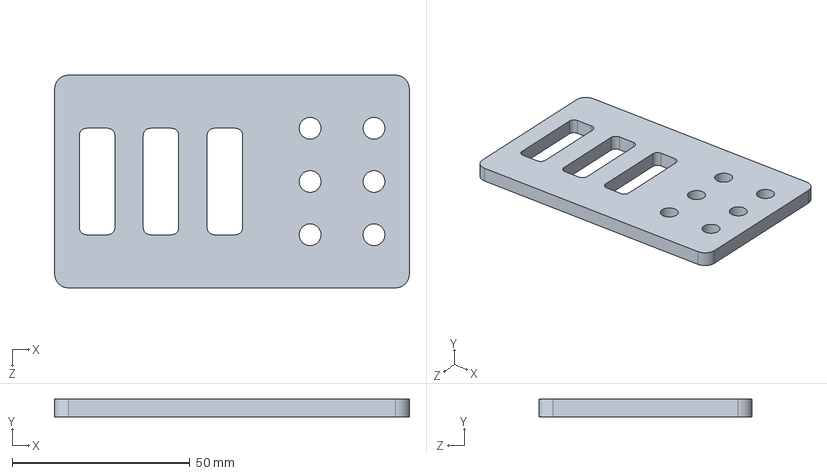
[picture p130: CAD file, 2020-11-13]
3D_models/Solidworks/下肢/固定/腰部綁帶固定片[01_v1.0].SLDPRT
100.0 x 5.00 x 60.0 mm
