ziteh/LEAP/3D_models/Solidworks/下肢/固定/腳踝軸承軸心[01_v1.0].SLDPRT

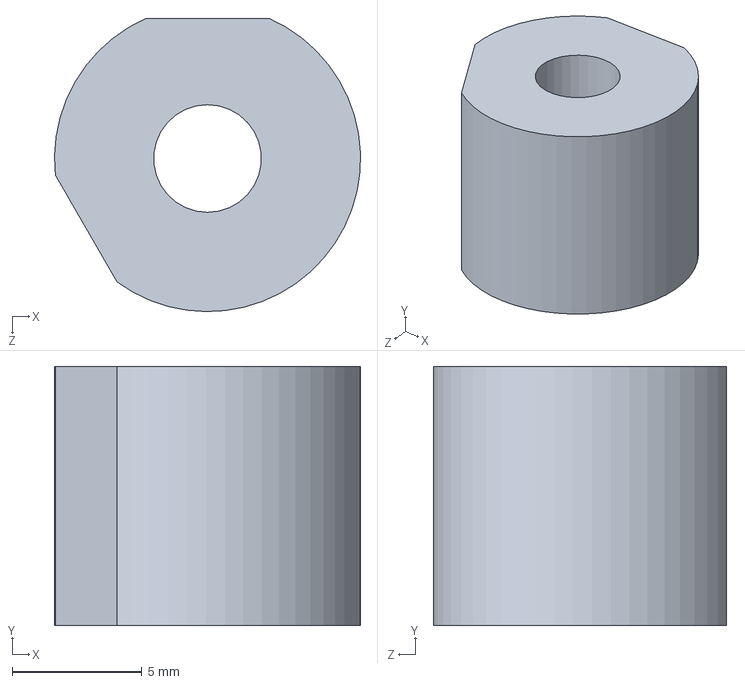
[picture p131: CAD file, 2020-11-13]
3D_models/Solidworks/下肢/固定/腳踝軸承軸心[01_v1.0].SLDPRT
11.8 x 10.0 x 11.3 mm
