ziteh/LEAP/3D_models/Solidworks/下肢/固定/膝關節馬達固定板-01_v2.0.SLDPRT

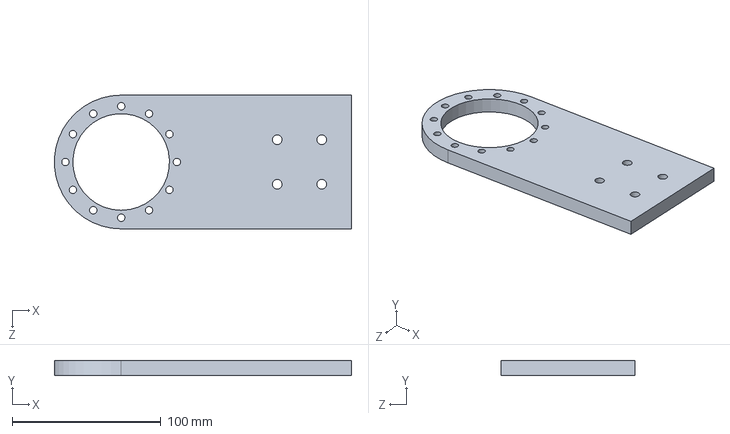
[picture p132: CAD file, 2020-11-13]
3D_models/Solidworks/下肢/固定/膝關節馬達固定板-01_v2.0.SLDPRT
199.9 x 10.0 x 90.0 mm
