ziteh/LEAP/3D_models/Solidworks/下肢/固定/腳底板固定片[01_v1.0].SLDPRT

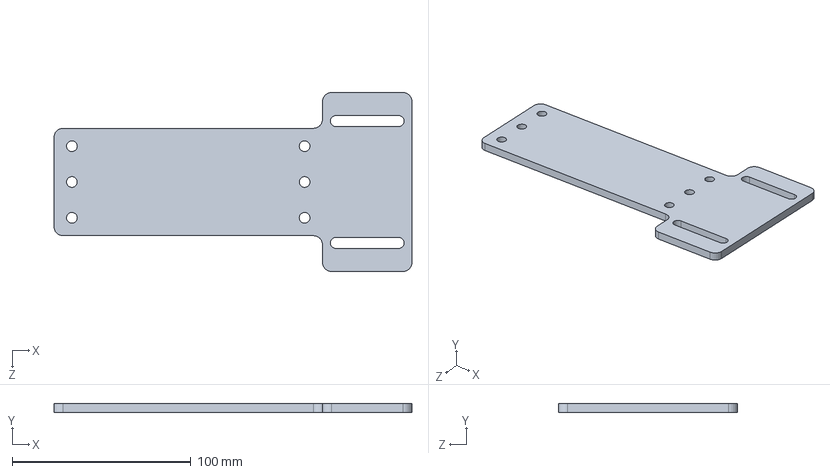
[picture p133: CAD file, 2020-11-13]
3D_models/Solidworks/下肢/固定/腳底板固定片[01_v1.0].SLDPRT
200.0 x 5.00 x 100.0 mm
