ziteh/LEAP/3D_models/Solidworks/下肢/固定/HD軸向軸承固定片(01_v3.0).SLDPRT

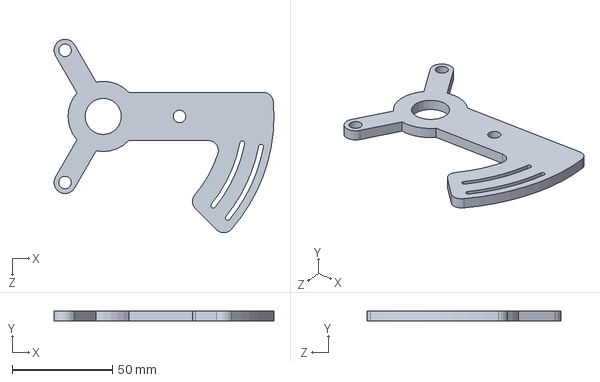
[picture p134: CAD file, 2020-11-13]
3D_models/Solidworks/下肢/固定/HD軸向軸承固定片(01_v3.0).SLDPRT
109.5 x 5.00 x 96.3 mm
