ziteh/LEAP/3D_models/Solidworks/下肢/固定/膝關節馬達固定板-02_v1.0.SLDPRT

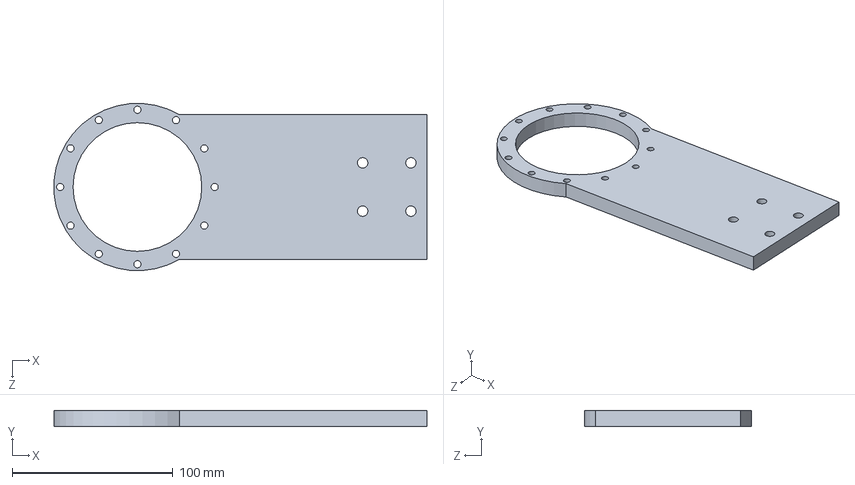
[picture p135: CAD file, 2020-11-13]
3D_models/Solidworks/下肢/固定/膝關節馬達固定板-02_v1.0.SLDPRT
231.8 x 10.0 x 103.8 mm
