ziteh/LEAP/3D_models/Solidworks/下肢/固定/EC90flot固定片(01_v3.2).SLDPRT

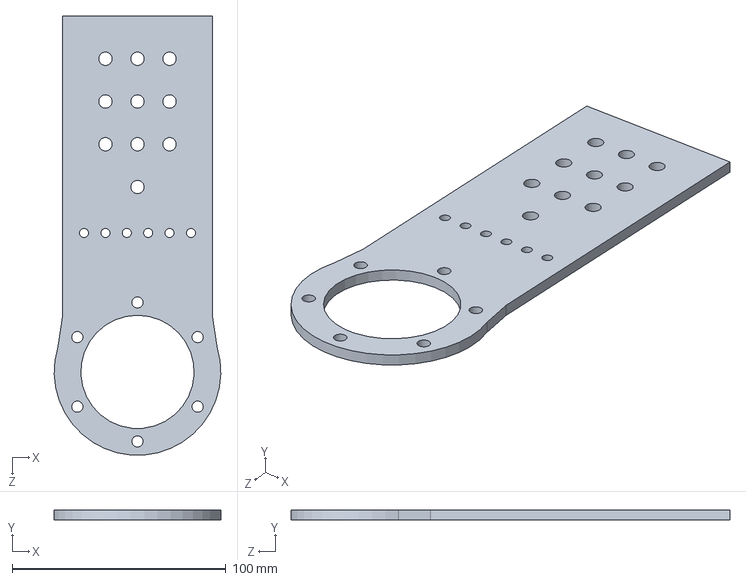
[picture p136: CAD file, 2020-11-13]
3D_models/Solidworks/下肢/固定/EC90flot固定片(01_v3.2).SLDPRT
78.0 x 4.50 x 205.4 mm
