ziteh/LEAP/3D_models/Solidworks/下肢/固定/主電路板固定片[01_v1.0].SLDPRT

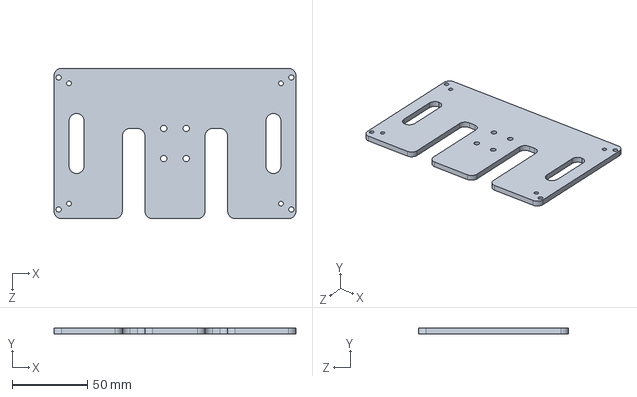
[picture p137: CAD file, 2020-11-13]
3D_models/Solidworks/下肢/固定/主電路板固定片[01_v1.0].SLDPRT
161.0 x 4.00 x 100.0 mm
