ziteh/LEAP/pcb/LEAP.sch

## KiCad design pcb/LEAP.sch (2020-11-13)

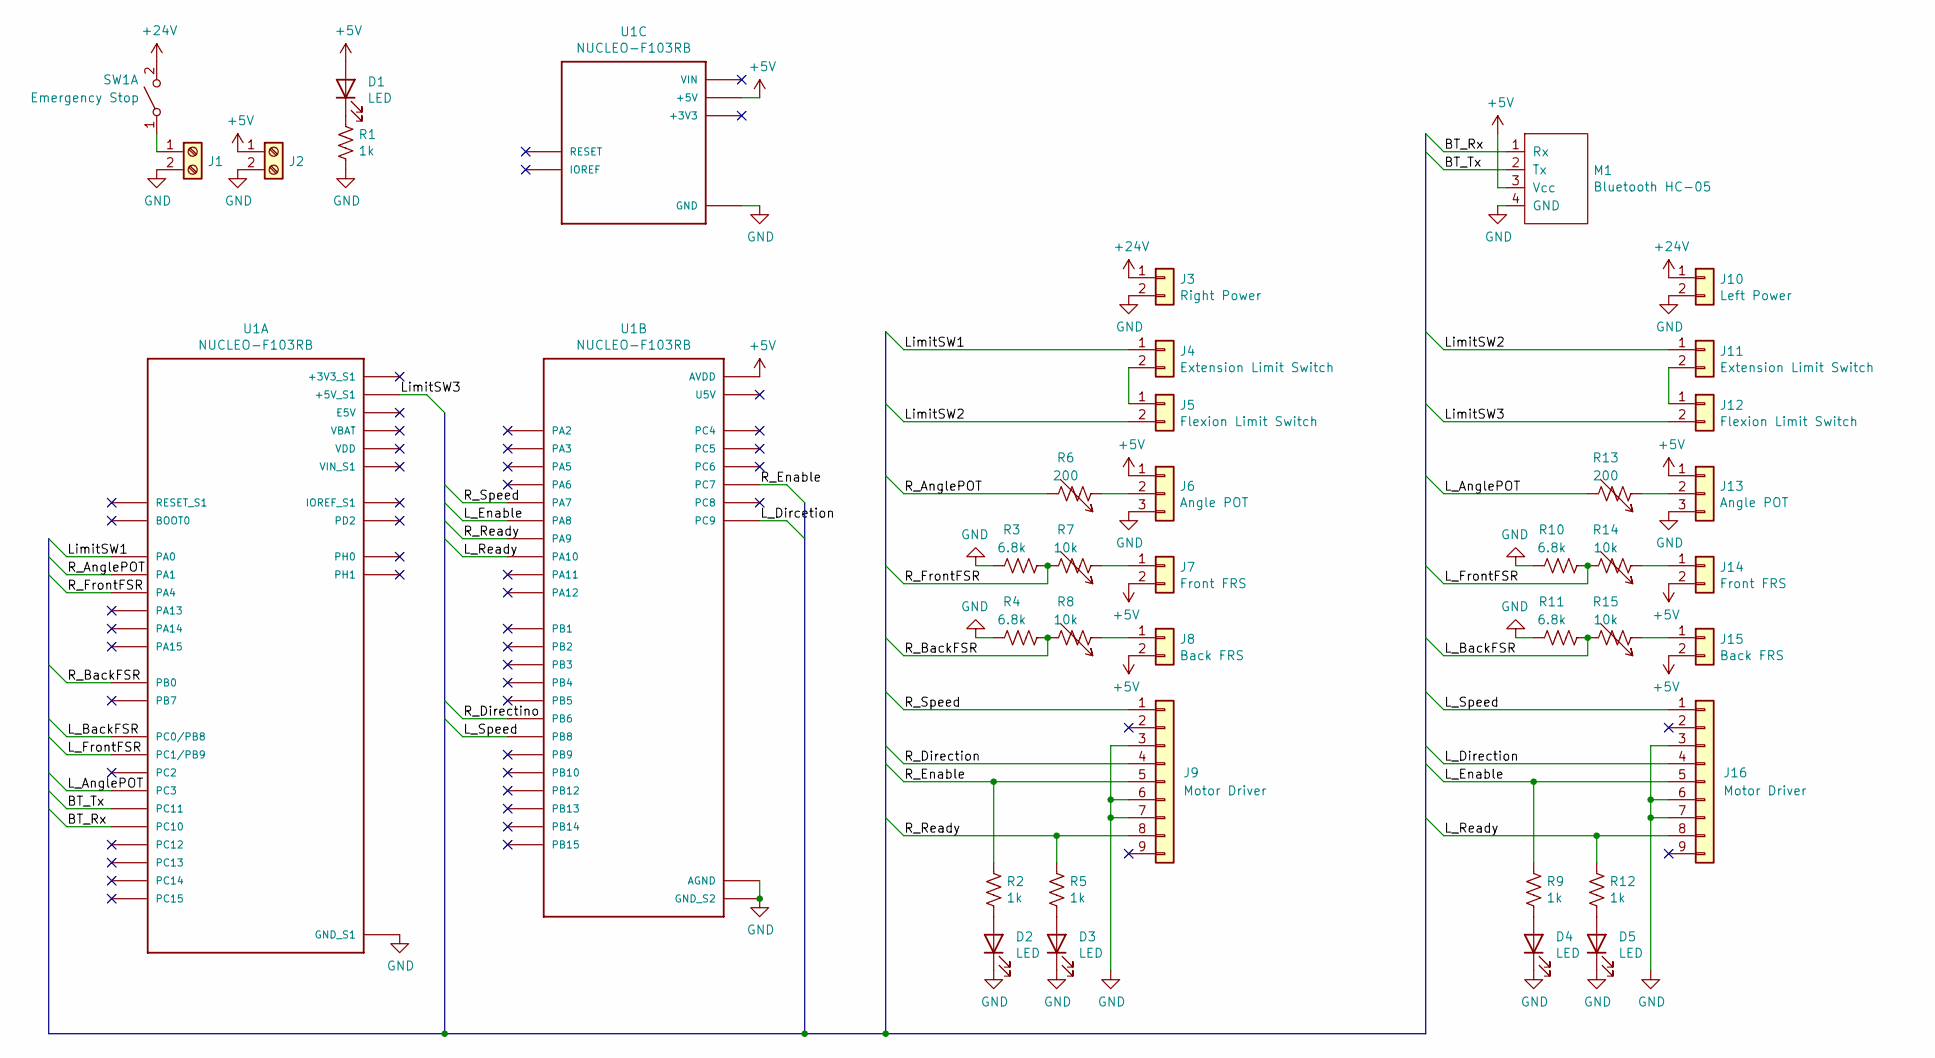
[picture p139: schematic LEAP.sch]

Parts:
D1, D2, D3, D4, D5: LED
J1, J2: Screw_Terminal_01x02
J3: Right Power
J4, J11: Extension Limit Switch
J5, J12: Flexion Limit Switch
J6, J13: Angle POT
J7, J14: Front FRS
J8, J15: Back FRS
J9, J16: Motor Driver
J10: Left Power
M1: Bluetooth HC-05
R1, R2, R5, R9, R12: 1k
R3, R4, R10, R11: 6.8k
R6, R13: 200
R7, R8, R14, R15: 10k
SW1: Emergency Stop
U1: NUCLEO-F103RB; ST_NUCLEO-F401RE

Connections:
+5V: D1.2 (A), J2.1, J6.1, J7.2, J8.2, J13.1, J14.2, J15.2, M1.3 (Vcc), U1.CN6_5 (+5V), U1.CN10_7 (AVDD)
+24V: J3.1, J10.1, SW1.2 (B)
BT_Rx: M1.1 (Rx), U1.CN7_1 (PC10)
BT_Tx: M1.2 (Tx), U1.CN7_2 (PC11)
GND: D2.1 (K), D3.1 (K), D4.1 (K), D5.1 (K), J1.2, J2.2, J3.2, J6.3, J9.3, J9.6, J9.7, J10.2, J13.3, J16.3, J16.6, J16.7, M1.4 (GND), R1.2, R3.2, R4.2, R10.2, R11.2, U1.CN6_6 (GND), U1.CN6_7 (GND), U1.CN7_8 (GND_S1), U1.CN7_19 (GND_S1), U1.CN7_20 (GND_S1), U1.CN7_22 (GND_S1), U1.CN10_9 (GND_S2), U1.CN10_20 (GND_S2), U1.CN10_32 (AGND)
L_AnglePOT: R13.2, U1.CN7_37 (PC3)
L_BackFSR: R11.1, R15.2, U1.CN7_38 (PC0/PB8)
L_Dircetion: U1.CN10_1 (PC9)
L_Direction: J16.4
L_Enable: J16.5, R9.1, U1.CN10_23 (PA8)
L_FrontFSR: R10.1, R14.2, U1.CN7_36 (PC1/PB9)
L_Ready: J16.8, R12.1, U1.CN10_33 (PA10)
L_Speed: J16.1, U1.CN10_3 (PB8)
LimitSW1: J4.1, U1.CN7_28 (PA0)
LimitSW2: J5.2, J11.1
LimitSW3: J12.2, U1.CN7_18 (+5V_S1)
unnamed: D1.1 (K), R1.1
unnamed: D2.2 (A), R2.2
unnamed: D3.2 (A), R5.2
unnamed: D4.2 (A), R9.2
unnamed: D5.2 (A), R12.2
unnamed: J1.1, SW1.1 (A)
unnamed: J4.2, J5.1
unnamed: J6.2, R6.1
unnamed: J7.1, R7.1
unnamed: J8.1, R8.1
unnamed: J11.2, J12.1
unnamed: J13.2, R13.1
unnamed: J14.1, R14.1
unnamed: J15.1, R15.1
R_AnglePOT: R6.2, U1.CN7_30 (PA1)
R_BackFSR: R4.1, R8.2, U1.CN7_34 (PB0)
R_Directino: U1.CN10_17 (PB6)
R_Direction: J9.4
R_Enable: J9.5, R2.1, U1.CN10_19 (PC7)
R_FrontFSR: R3.1, R7.2, U1.CN7_32 (PA4)
R_Ready: J9.8, R5.1, U1.CN10_21 (PA9)
R_Speed: J9.1, U1.CN10_15 (PA7)
