ziteh/LEAP/stm32/PoweredExoskeleton-01_C/src/main.h

/**
  ******************************************************************************
  * @file    main.h 
  * @author  MCD Application Team
  * @version V1.0.0
  * @date    11-February-2014
  * @brief   Header for main.c module
  ******************************************************************************
  * @attention
  *
  * <h2><center>&copy; COPYRIGHT 2014 STMicroelectronics</center></h2>
  *
  * Licensed under MCD-ST Liberty SW License Agreement V2, (the "License");
  * You may not use this file except in compliance with the License.
  * You may obtain a copy of the License at:
  *
  *        http://www.st.com/software_license_agreement_liberty_v2
  *
  * Unless required by applicable law or agreed to in writing, software 
  * distributed under the License is distributed on an "AS IS" BASIS, 
  * WITHOUT WARRANTIES OR CONDITIONS OF ANY KIND, either express or implied.
  * See the License for the specific language governing permissions and
  * limitations under the License.
  *
  ******************************************************************************
  */
  
/* Define to prevent recursive inclusion -------------------------------------*/
#ifndef __MAIN_H
#define __MAIN_H

/* Includes ------------------------------------------------------------------*/
#include "stm32f1xx_nucleo.h"

/* Exported types ------------------------------------------------------------*/
/* Exported constants --------------------------------------------------------*/
/* Exported macro ------------------------------------------------------------*/
/* Exported functions ------------------------------------------------------- */
void TimingDelay_Decrement(void);
void Delay(__IO uint32_t nTime);
void SendStatus(void);
void MotorCtrl(uint8_t Motor, uint8_t Status, uint8_t Direction, uint16_t Speed);
void MotorAccelerationCtrl(uint8_t Motor, uint16_t TargetSpeed);
char* Number_TO_String(uint16_t Number);
u8 PerMill_TO_Percentage(u16 PerMill);
void Delay_normal(__IO u32 nTime);

#endif /* __MAIN_H */

/************************ (C) COPYRIGHT STMicroelectronics *****END OF FILE****/
