ziteh/LEAP/stm32/PoweredExoskeleton-01_C/src/NVIC_Functions.h

/**
 ******************************************************************************
 * @file   		NVIC_Functions.h
 * @author  	Huang Tzu-Fu
 * 				National Formosa University
 * 				Department of Electronic Engineering
 * 				Intelligent Robot System Laboratory
 * @version 	V1.0.0
 * @date    	14-October-2019
 * @brief  		Header for NVIC_Functions.c module
 ******************************************************************************
 * @attention
 *
 * None
 *
 ******************************************************************************
 */

/* Define to prevent recursive inclusion -------------------------------------*/
#ifndef __NVIC_FUNCTIONS_H
#define __NVIC_FUNCTIONS_H

/* Includes ------------------------------------------------------------------*/
/* Exported types ------------------------------------------------------------*/
/* Exported constants --------------------------------------------------------*/
/* Exported macro ------------------------------------------------------------*/
/* Exported functions ------------------------------------------------------- */
void NVIC_Initialization(void);

#endif /* __NVIC_FUNCTIONS_H */

/********************************END OF FILE***********************************/
